pfanchri/Wordclock/Frontplatten/Glocke/File:Bell font awesome.svg - Wikimedia Commons.pdf

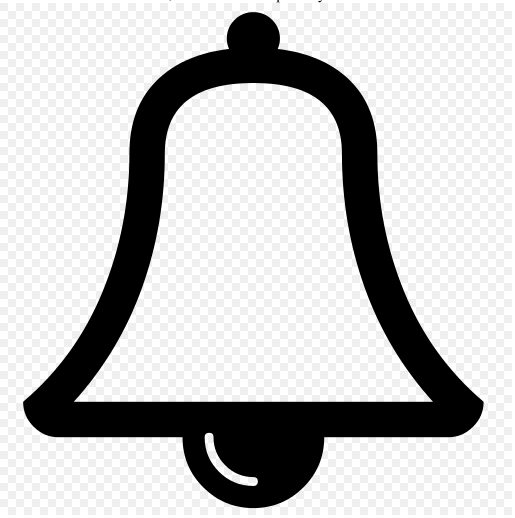
[picture p33: figure]

The source code of this SVG (https://commons.wikimedia.org/wiki/Help:SVG) is valid (https://validator.w3.org/check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). (https://validator.w3.org/check?ss=1)

This vector image (https://en.wikipedia.org/wiki/Vector_graphics) was created with Inkscape, (https://commons.wikimedia.org/wiki/Help:Inkscape) and then manually (https://en.wikipedia.org/wiki/Text_editor) edited.

# File:Bell font awesome.svg

From Wikimedia Commons, the free media repository

Size of this PNG preview of this SVG file: 512 × 512 pixels. (https://upload.wikimedia.org/wikipedia/commons/thumb/c/ca/Bell_font_awesome.svg/512px-Bell_font_awesome.svg.png)
Original file (https://upload.wikimedia.org/wikipedia/commons/c/ca/Bell_font_awesome.svg) (SVG file, nominally 512 × 512 pixels, file size: 2 KB)

This image rendered as PNG in other widths: 200px, (https://upload.wikimedia.org/wikipedia/commons/thumb/c/ca/Bell_font_awesome.svg/200px-Bell_font_awesome.svg.png) 500px, (https://upload.wikimedia.org/wikipedia/commons/thumb/c/ca/Bell_font_awesome.svg/500px-Bell_font_awesome.svg.png) 1000px, (https://upload.wikimedia.org/wikipedia/commons/thumb/c/ca/Bell_font_awesome.svg/1000px-Bell_font_awesome.svg.png) 2000px. (https://upload.wikimedia.org/wikipedia/commons/thumb/c/ca/Bell_font_awesome.svg/2000px-Bell_font_awesome.svg.png)

## Summary

Description | Icon extracted from [fortawesome.github.com/Font-Awesome/ Font-Awesome]

Date
Source | http://fortawesome.github.com/Font-Awesome/
Author | Dave Gandy
SVG development

## Licensing

This file is licensed under the Creative Commons (https://en.wikipedia.org/wiki/en:Creative_Commons) Attribution-Share Alike 3.0 Unported (https://creativecommons.org/licenses/by-sa/3.0/deed.en) license.

### Attribution: Font Awesome by Dave Gandy - http://fortawesome.github.com/Font-Awesome (http://fortawesome.github.com/Font-Awesome)

You are free:

Wikimedia Commons auf Deutsch (https://commons.wikimedia.org/wiki/File:Bell_font_awesome.svg#) | [x] (https://commons.wikimedia.org/wiki/File:Bell_font_awesome.svg#) Download (https://commons.wikimedia.org/wiki/File:Bell_font_awesome.svg#)
all sizes

Use this file (https://commons.wikimedia.org/wiki/File:Bell_font_awesome.svg#)
on the web

Use this file (https://commons.wikimedia.org/wiki/File:Bell_font_awesome.svg#)
on a wiki

Email a link (https://commons.wikimedia.org/wiki/File:Bell_font_awesome.svg#)
to this file

Information (https://commons.wikimedia.org/wiki/File:Bell_font_awesome.svg#)
about reusing

Open in Media Viewer (https://upload.wikimedia.org/wikipedia/commons/c/ca/Bell_font_awesome.svg)

to share – to copy, distribute and transmit the work to remix – to adapt the work

Under the following conditions:

attribution – You must attribute the work in the manner specified by the author or licensor (but not in any way that suggests that they endorse you or your use of the work).
share alike – If you alter, transform, or build upon this work, you may distribute the resulting work only under the same or similar license to this one.

[[Category:]]

## File history

Click on a date/time to view the file as it appeared at that time.

| Date/Time | Thumbnail | Dimensions | User | Comment
current | 20:30, 26 January 2013 (https://upload.wikimedia.org/wikipedia/commons/c/ca/Bell_font_awesome.svg) | | 512 × 512 (2 KB) | Kondicherry (https://commons.wikimedia.org/wiki/User:Kondicherry) (talk (https://commons.wikimedia.org/wiki/User_talk:Kondicherry) | contribs) (https://commons.wikimedia.org/wiki/Special:Contributions/Kondicherry) | VicuñaUploader 1.16

You cannot overwrite this file.

## File usage on Commons

The following page links to this file:

User:Kondicherry/gallery (https://commons.wikimedia.org/wiki/User:Kondicherry/gallery)

## Metadata

This file contains additional information, such as Exif (https://commons.wikimedia.org/wiki/Commons:Exif) metadata, probably added from the digital camera or scanner used to create or digitize it. If the file has been modified from its original state, some details may not fully reflect the modified file. The timestamp is only as accurate as the clock in the camera, and it may be completely wrong.

Retrieved from "https://commons.wikimedia.org/w/index.php?title=File:Bell_font_awesome.svg&oldid=144734182"

Categories: (https://commons.wikimedia.org/wiki/Special:Categories) Font-Awesome icons (https://commons.wikimedia.org/wiki/Category:Font-Awesome_icons) Bell icons (https://commons.wikimedia.org/wiki/Category:Bell_icons)

This page was last modified on 30 December 2014, at 15:17.
Text is available under the Creative Commons Attribution-ShareAlike License; (https://creativecommons.org/licenses/by-sa/3.0/) additional terms may apply. By using this site, you agree to the Terms of Use (https://wikimediafoundation.org/wiki/Terms_of_Use) and Privacy Policy. (https://wikimediafoundation.org/wiki/Privacy_policy)
