pfanchri/Wordclock/CAD/Bilder/Bildschirmfoto 2015-12-24 um 15.16.03.png

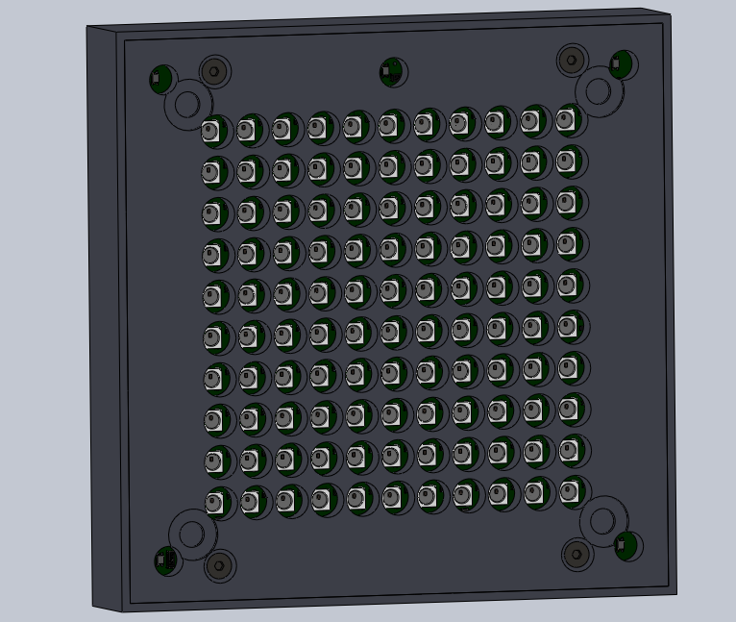
CAD/Bilder/Bildschirmfoto 2015-12-24 um 15.16.03.png
