pfanchri/Wordclock/CAD/Platine/Bauteile/importiert/ldr-cell-5mm-1.snapshot.6/Renderings/5mm-LDR-thru-hole-leaded.jpg

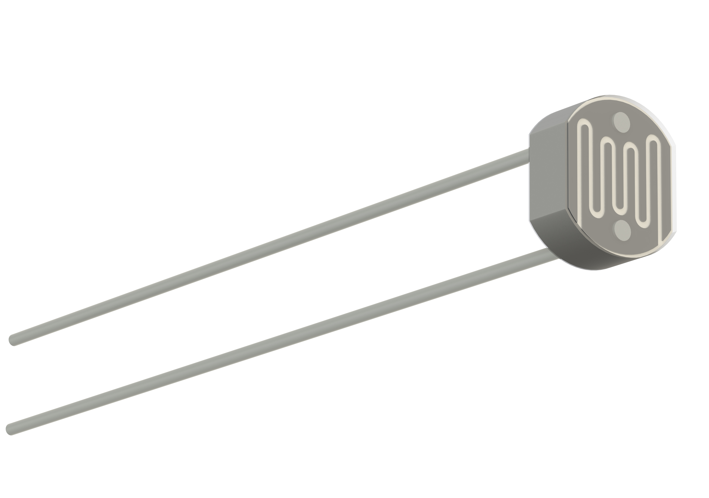
CAD/Platine/Bauteile/importiert/ldr-cell-5mm-1.snapshot.6/Renderings/5mm-LDR-thru-hole-leaded.jpg
