pfanchri/Wordclock/CAD/Platine/Bauteile/importiert/ldr-cell-5mm-1.snapshot.6/Renderings/LDR cell thru-hole leaded.jpg

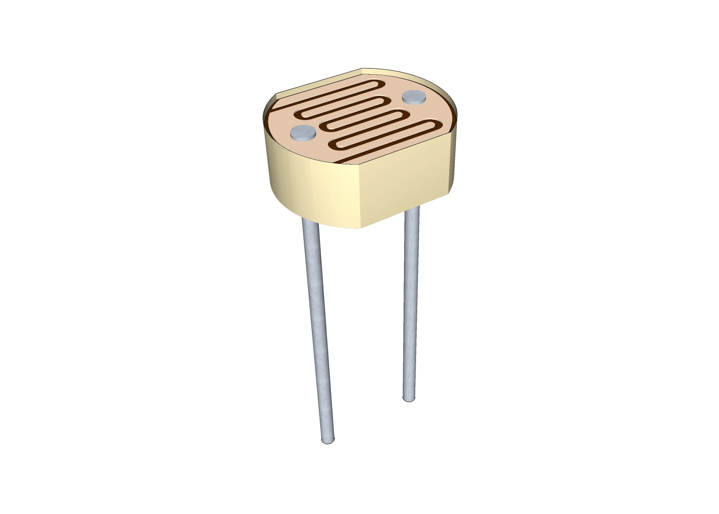
CAD/Platine/Bauteile/importiert/ldr-cell-5mm-1.snapshot.6/Renderings/LDR cell thru-hole leaded.jpg
