pfanchri/Wordclock/CAD/Platine/Bauteile/importiert/to220-to220ab-1.snapshot.5/Renderings/IMG_001.JPG

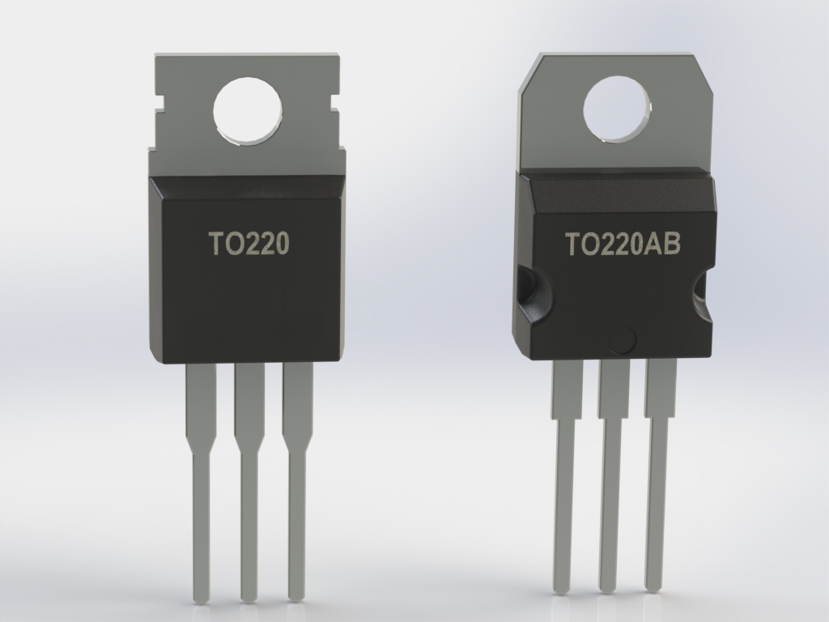
CAD/Platine/Bauteile/importiert/to220-to220ab-1.snapshot.5/Renderings/IMG_001.JPG
