pfanchri/Wordclock/Dokumentationen/Dokumentation/Bilder/SW1.png

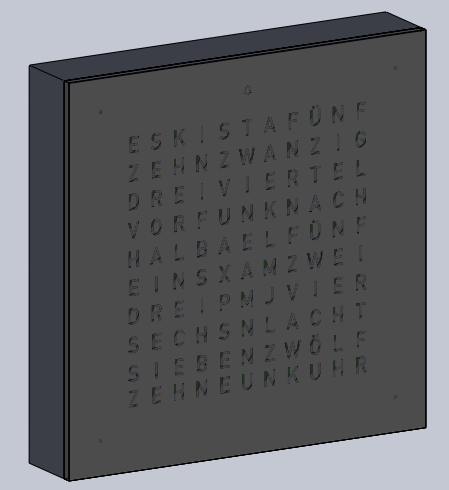
Dokumentationen/Dokumentation/Bilder/SW1.png
