pfanchri/Wordclock/Dokumentationen/Projektpräsentation/Anordnung3.png

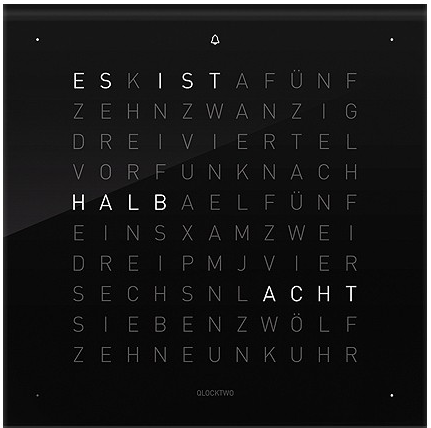
Dokumentationen/Projektpräsentation/Anordnung3.png
