pfanchri/Wordclock/Dokumentationen/Projektpräsentation/EagleL1.png

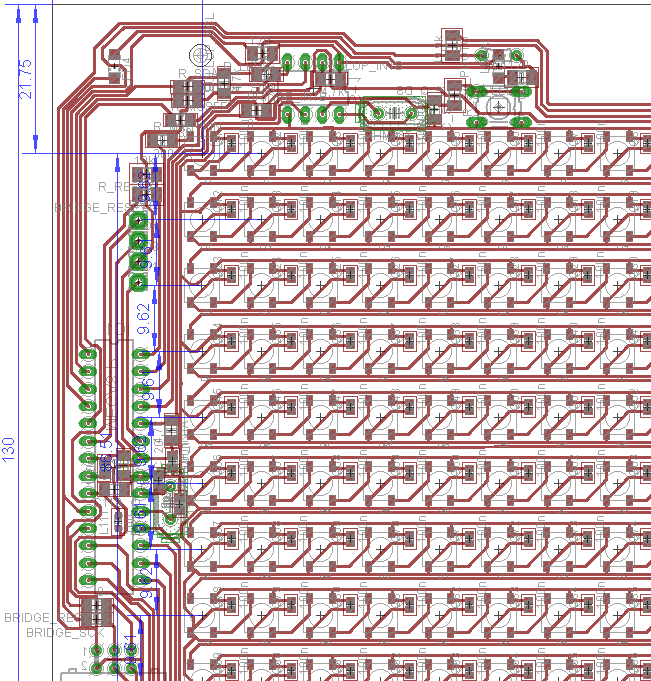
Dokumentationen/Projektpräsentation/EagleL1.png
