pfanchri/Wordclock/Dokumentationen/Projektpräsentation/EagleS2.png

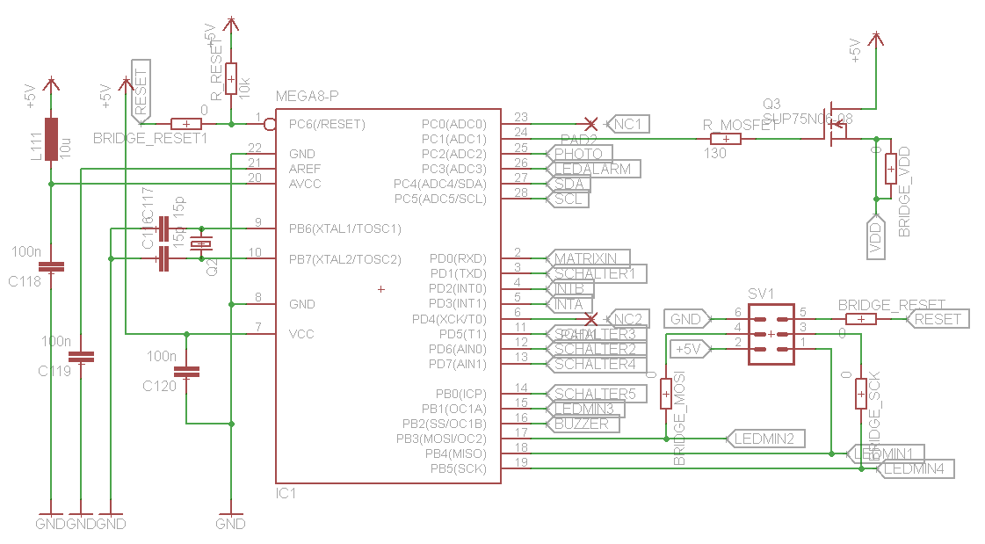
Dokumentationen/Projektpräsentation/EagleS2.png
