pfanchri/Wordclock/Dokumentationen/Projektpräsentation/SW3.png

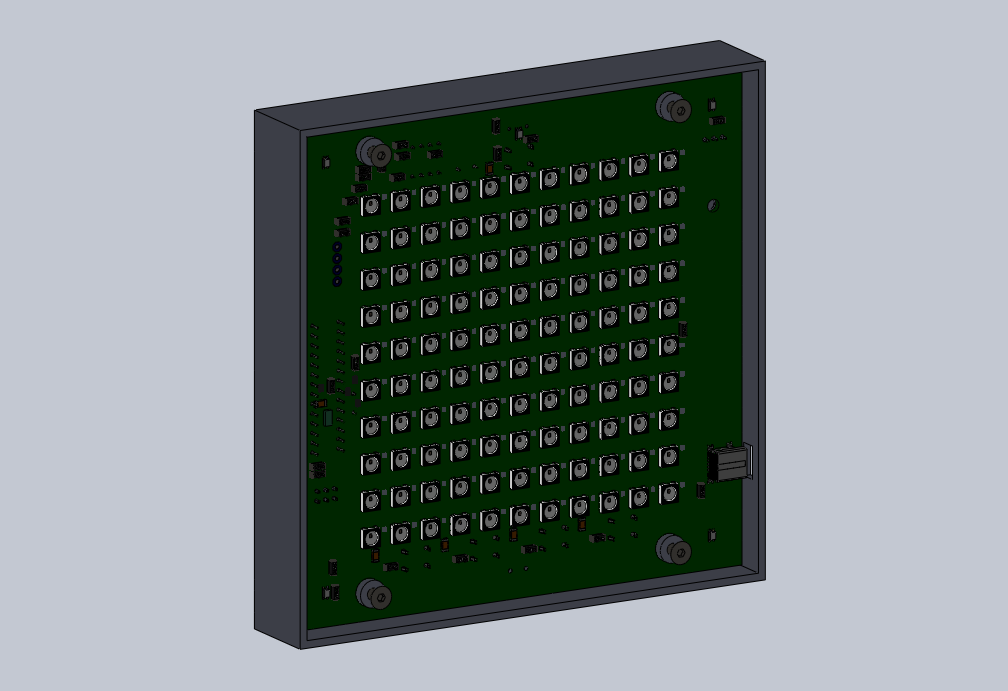
Dokumentationen/Projektpräsentation/SW3.png
