pfanchri/Wordclock/Frontplatten/Frontplatte Binär/Binäruhr/00addbfca08bbe93f4dcbb11746f65bc_1194087881.jpg

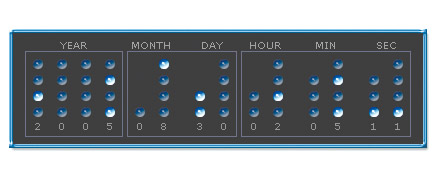
Frontplatten/Frontplatte Binär/Binäruhr/00addbfca08bbe93f4dcbb11746f65bc_1194087881.jpg
