pfanchri/Wordclock/Frontplatten/Frontplatte Binär/Binäruhr/68-847-74_2-original.png

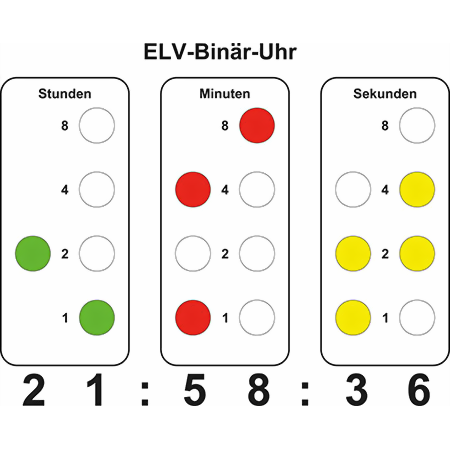
Frontplatten/Frontplatte Binär/Binäruhr/68-847-74_2-original.png
