pfanchri/Wordclock/Frontplatten/Frontplatte Binär/Binäruhr/500px-Binary_clock.png

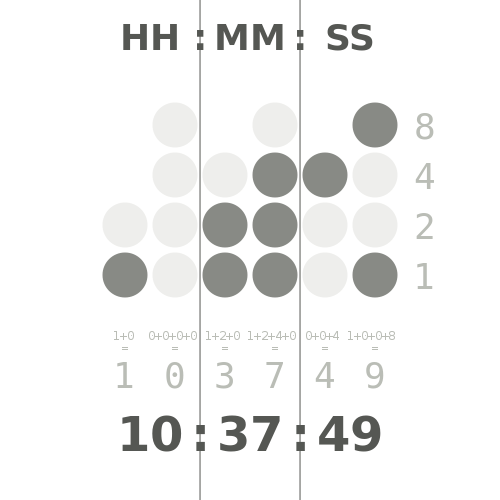
Frontplatten/Frontplatte Binär/Binäruhr/500px-Binary_clock.png
