pfanchri/Wordclock/Frontplatten/Wordclock-01.png

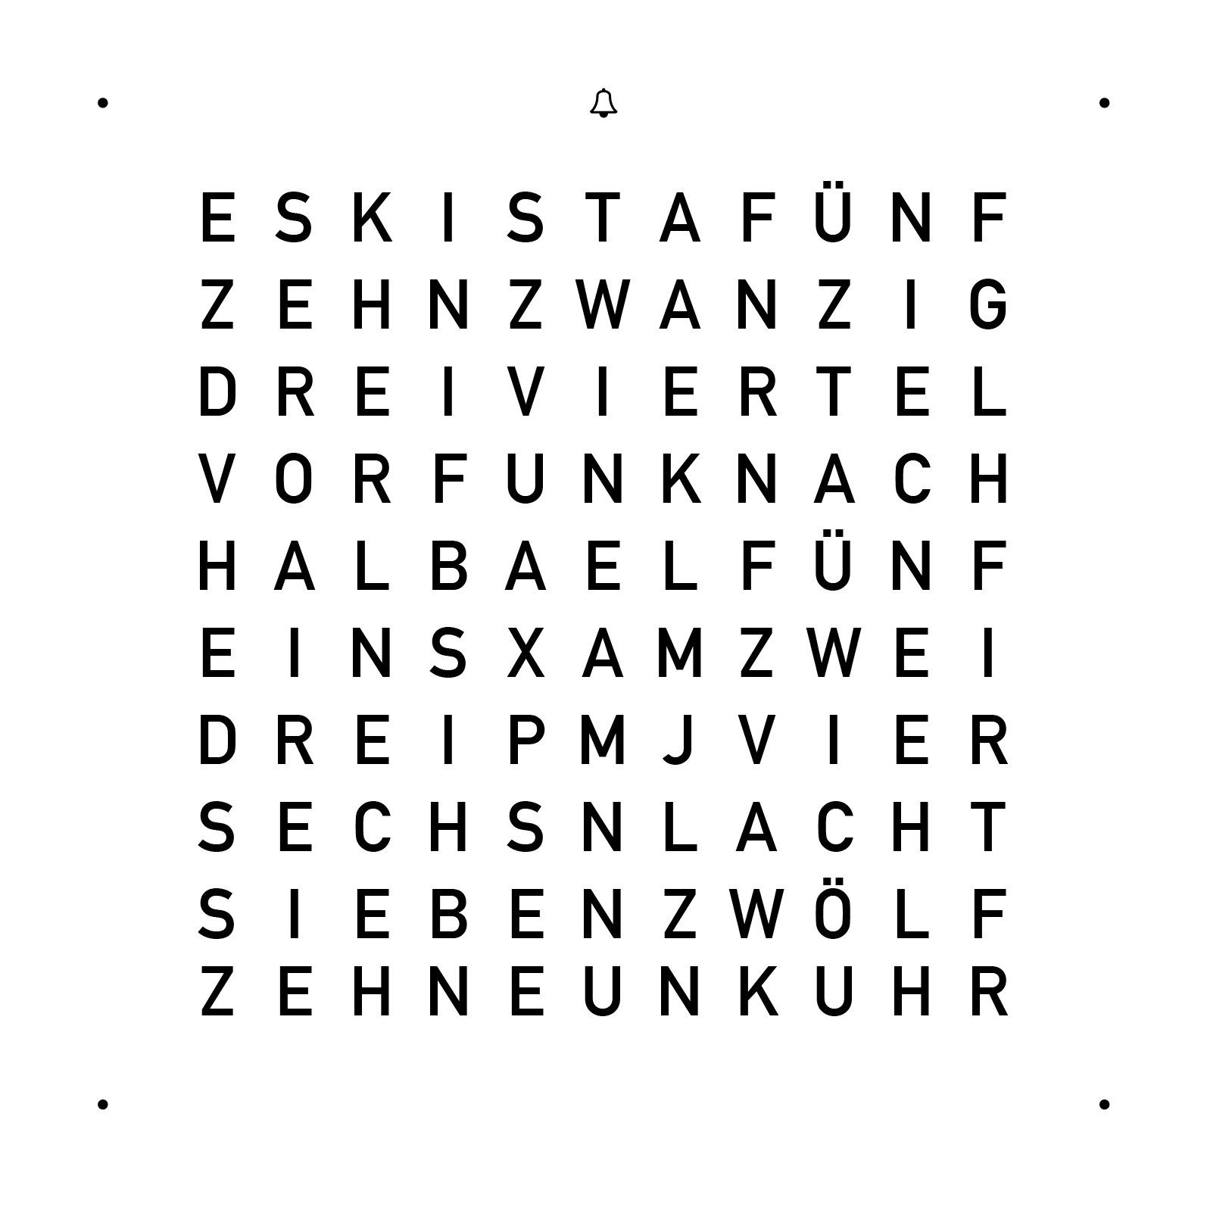
Frontplatten/Wordclock-01.png
