pfanchri/Wordclock/Pflichtenheft/images/0001.jpg

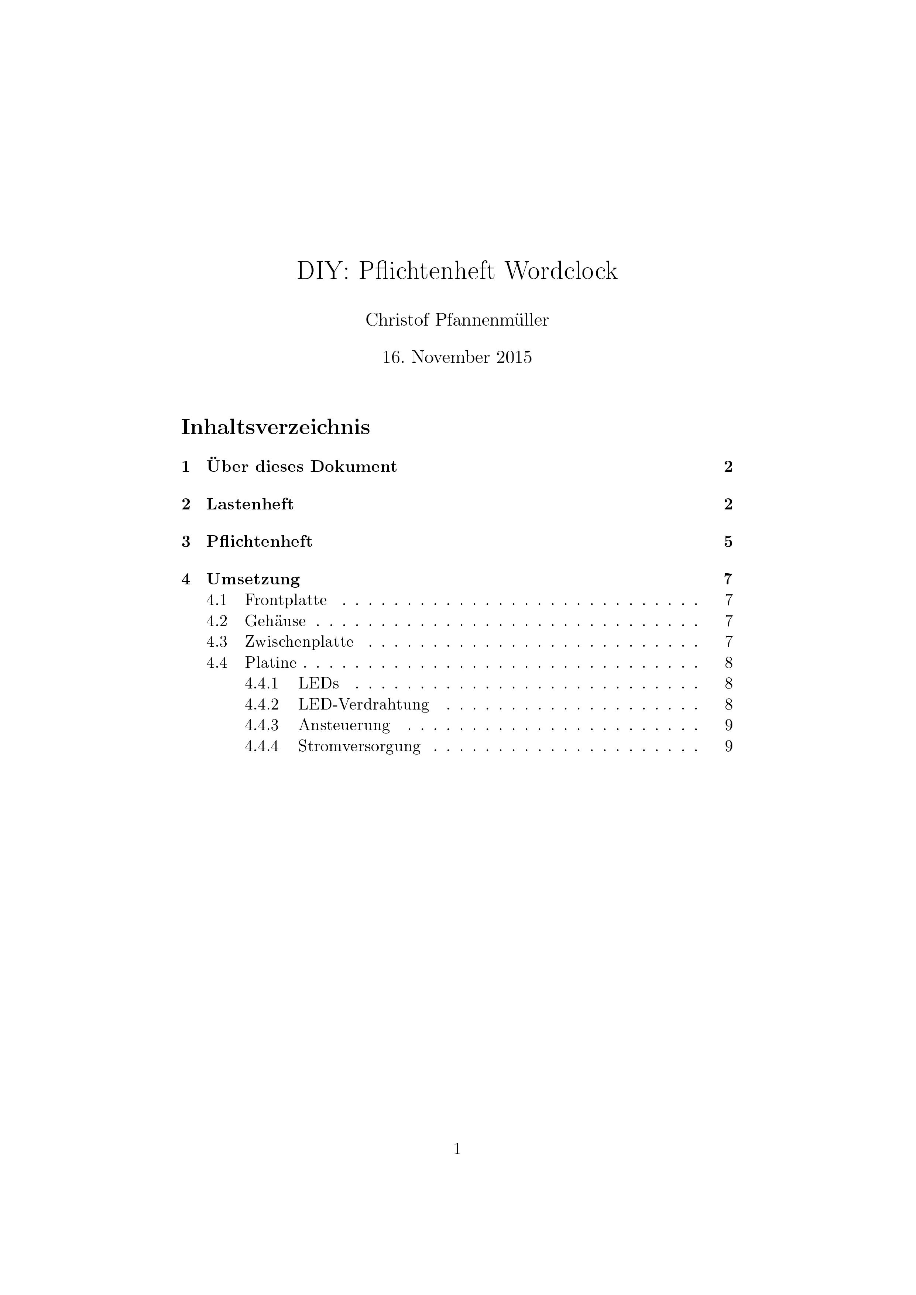
Pflichtenheft/images/0001.jpg
