pfanchri/Wordclock/Pflichtenheft/images/0002.jpg

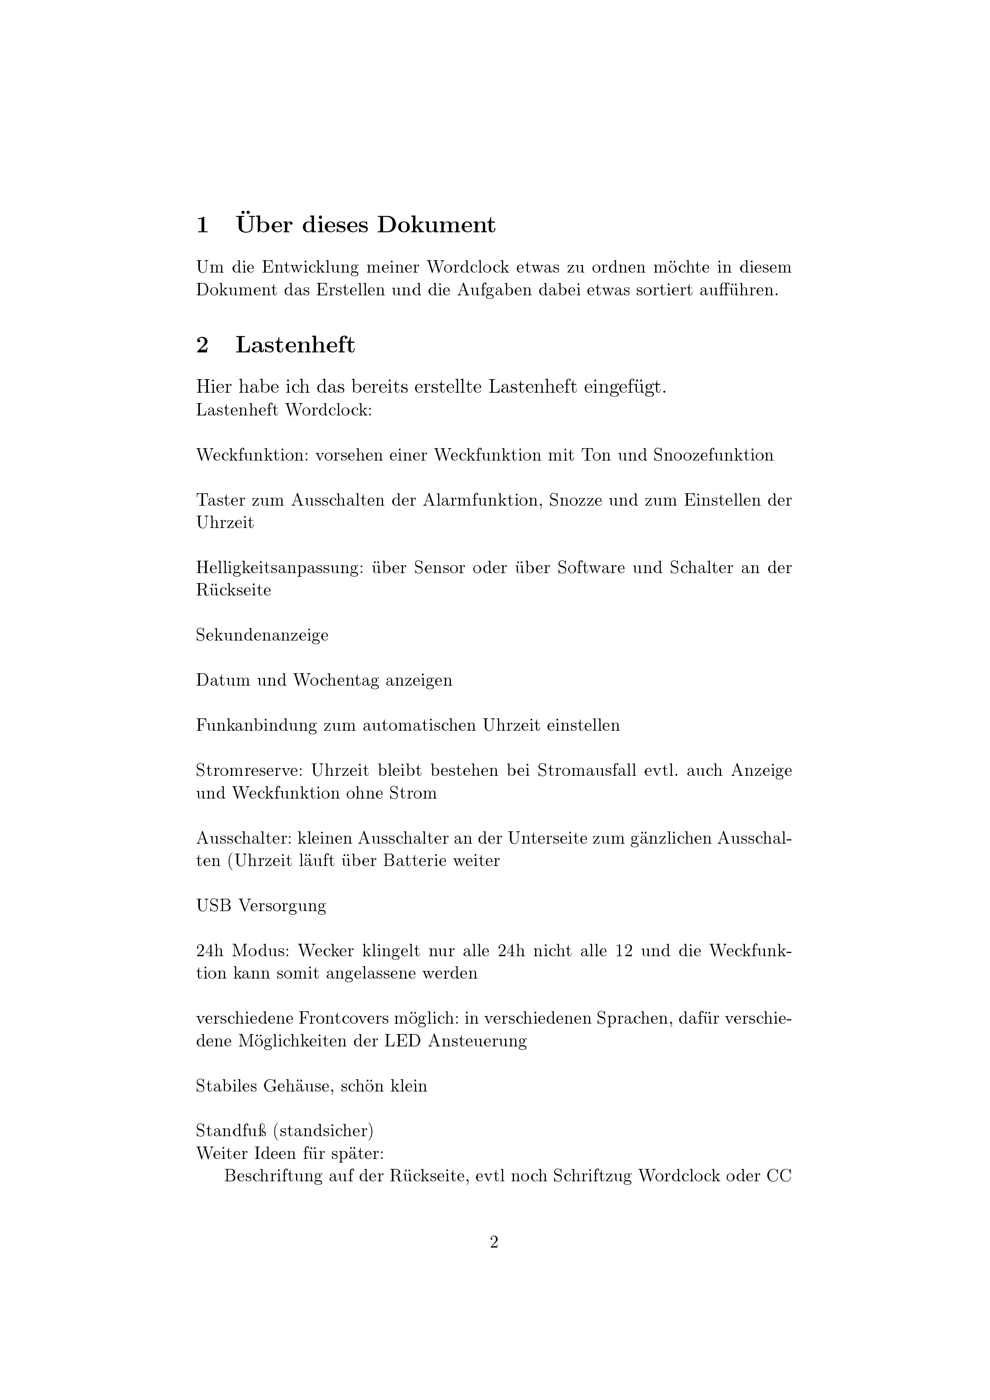
Pflichtenheft/images/0002.jpg
