pfanchri/Wordclock/Pflichtenheft/images/0005.jpg

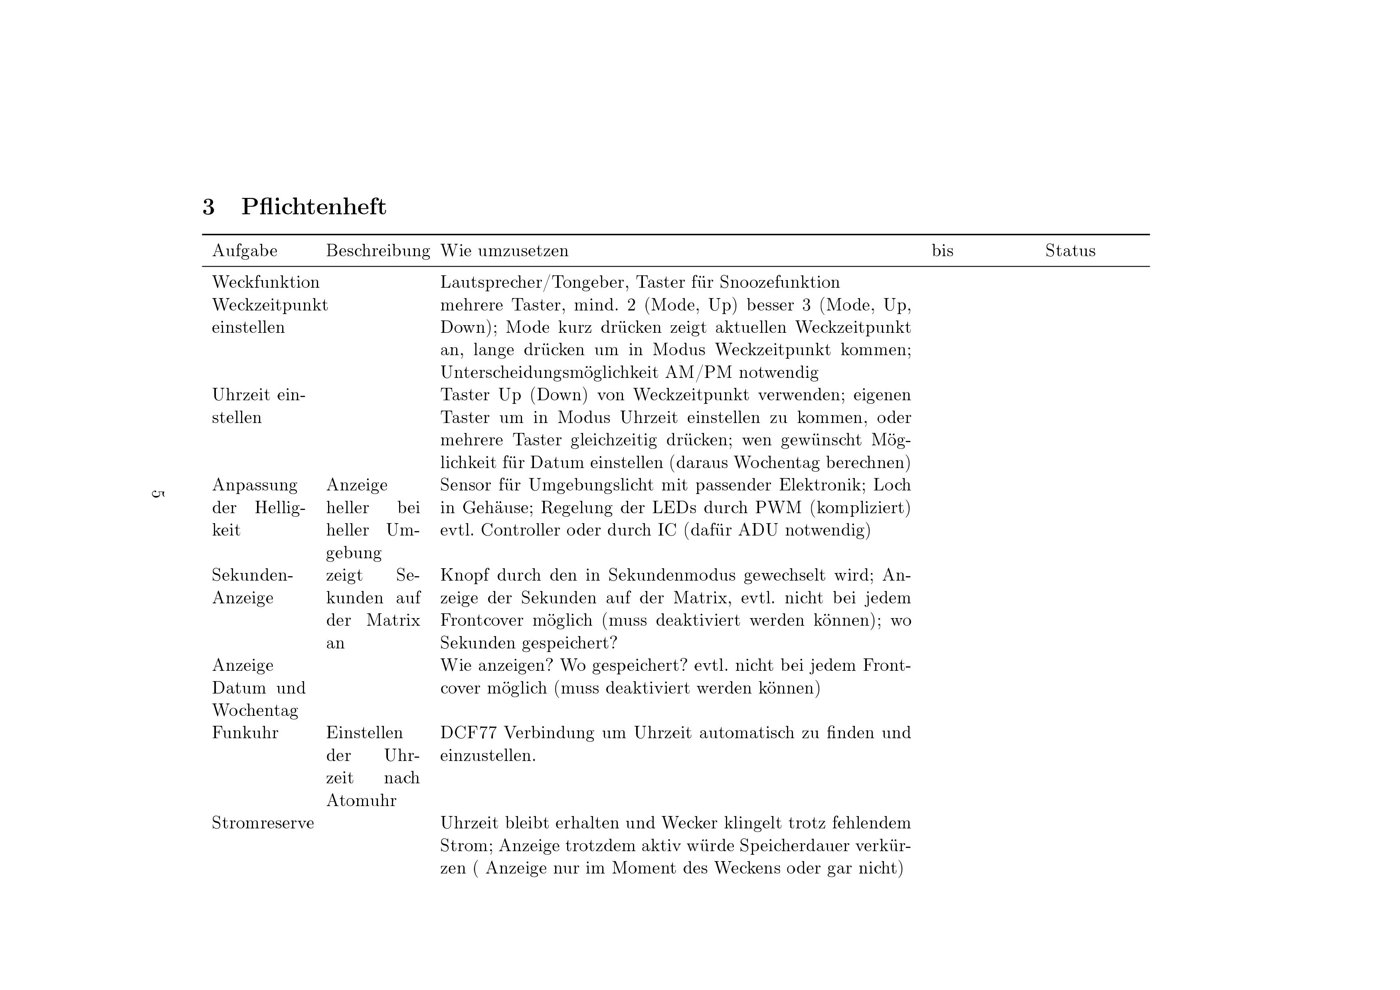
Pflichtenheft/images/0005.jpg
