pfanchri/Wordclock/Pflichtenheft/images/0006.jpg

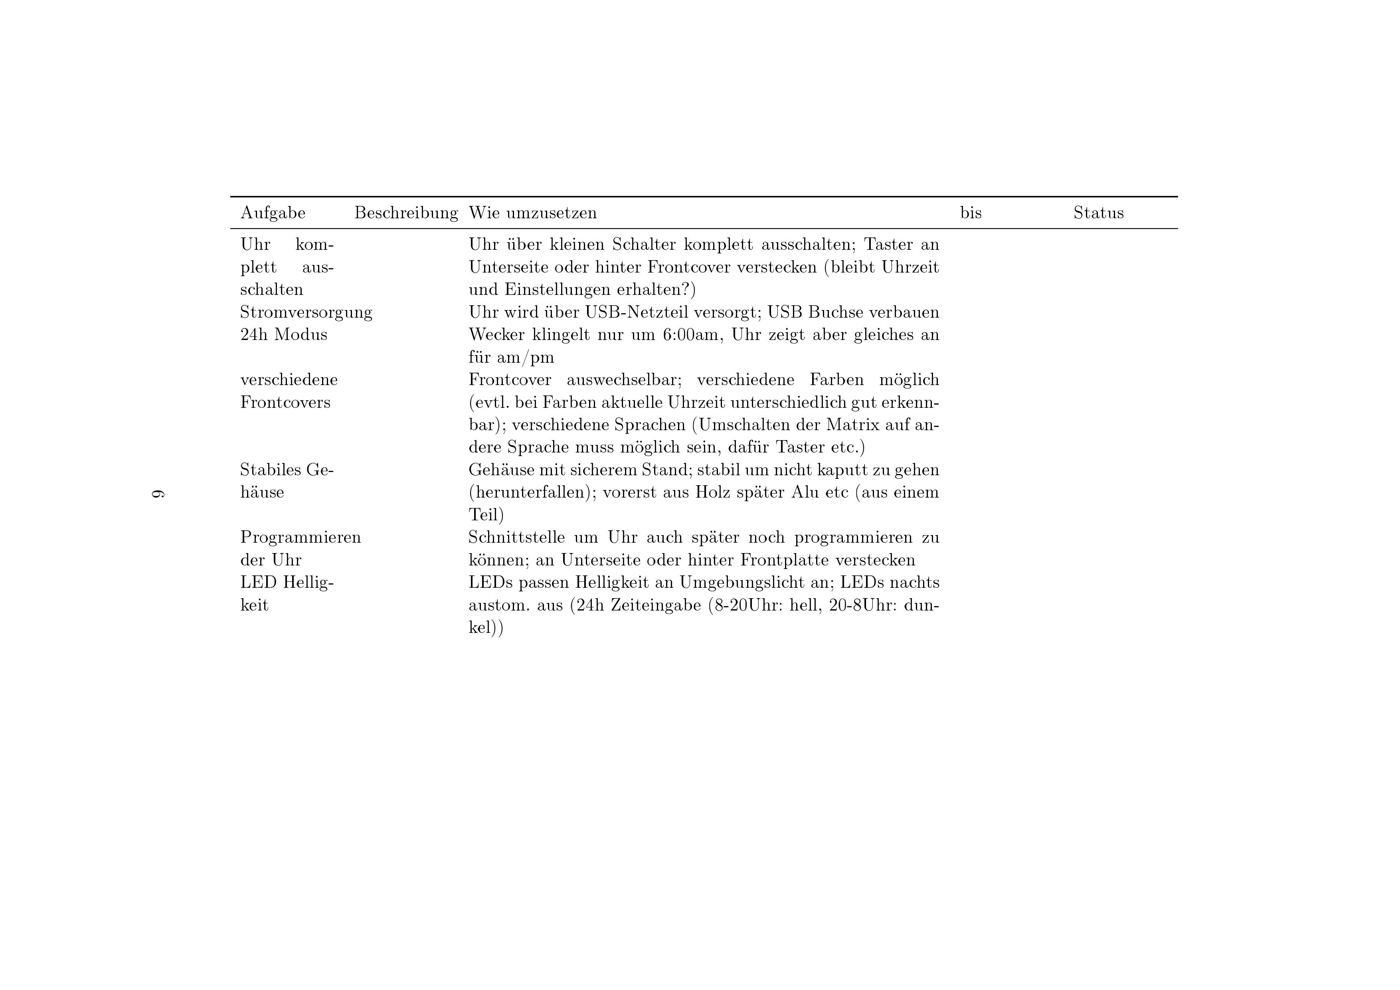
Pflichtenheft/images/0006.jpg
