pfanchri/Wordclock/Pflichtenheft/images/0007.jpg

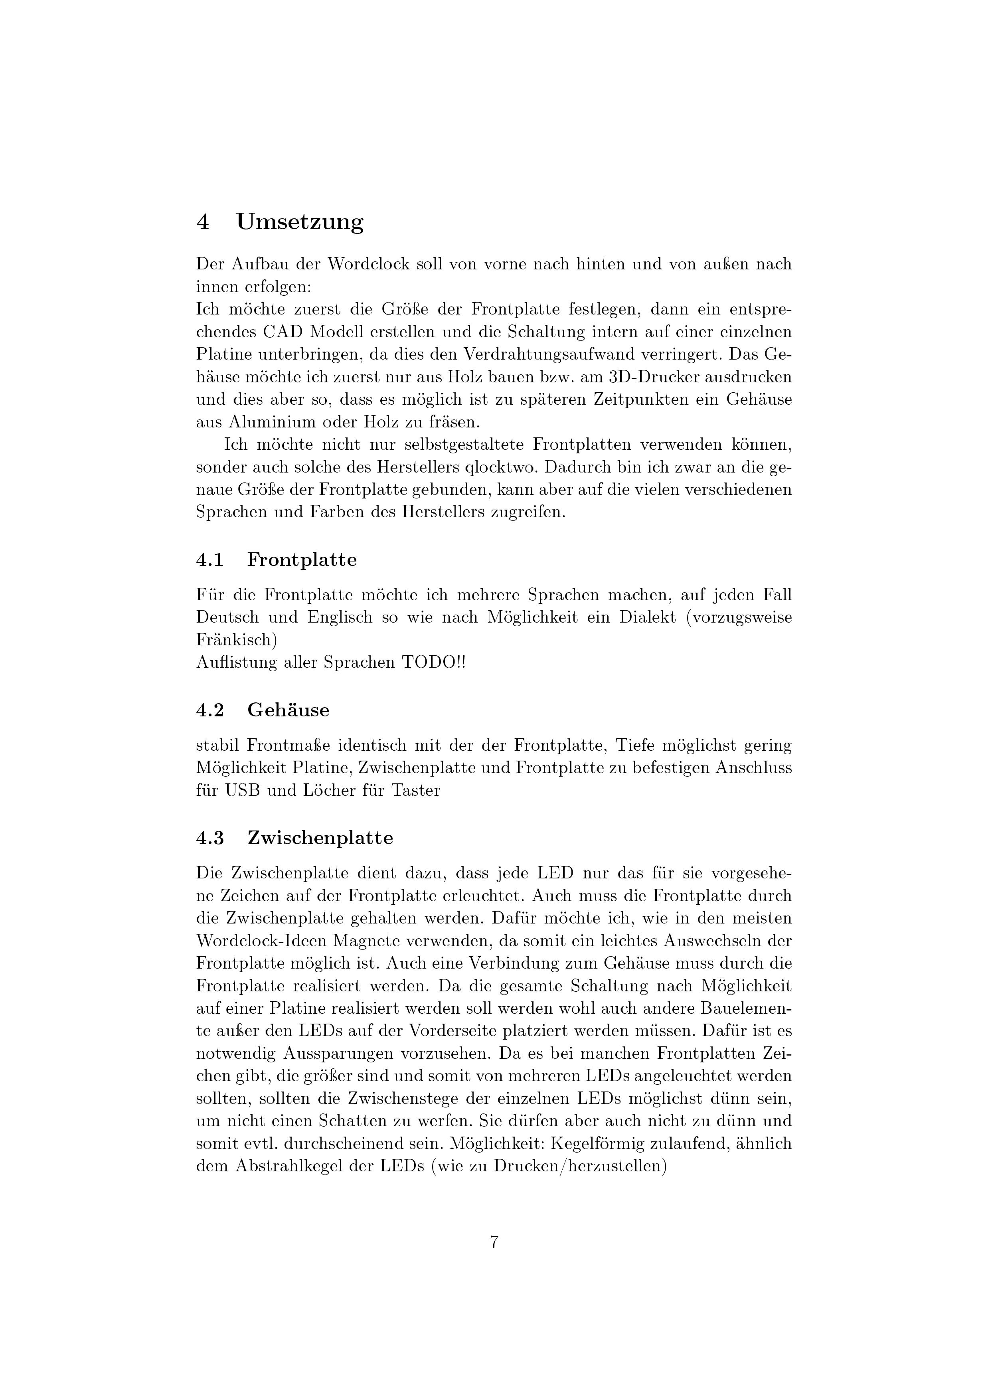
Pflichtenheft/images/0007.jpg
