pfanchri/Wordclock/Pflichtenheft/images/0008.jpg

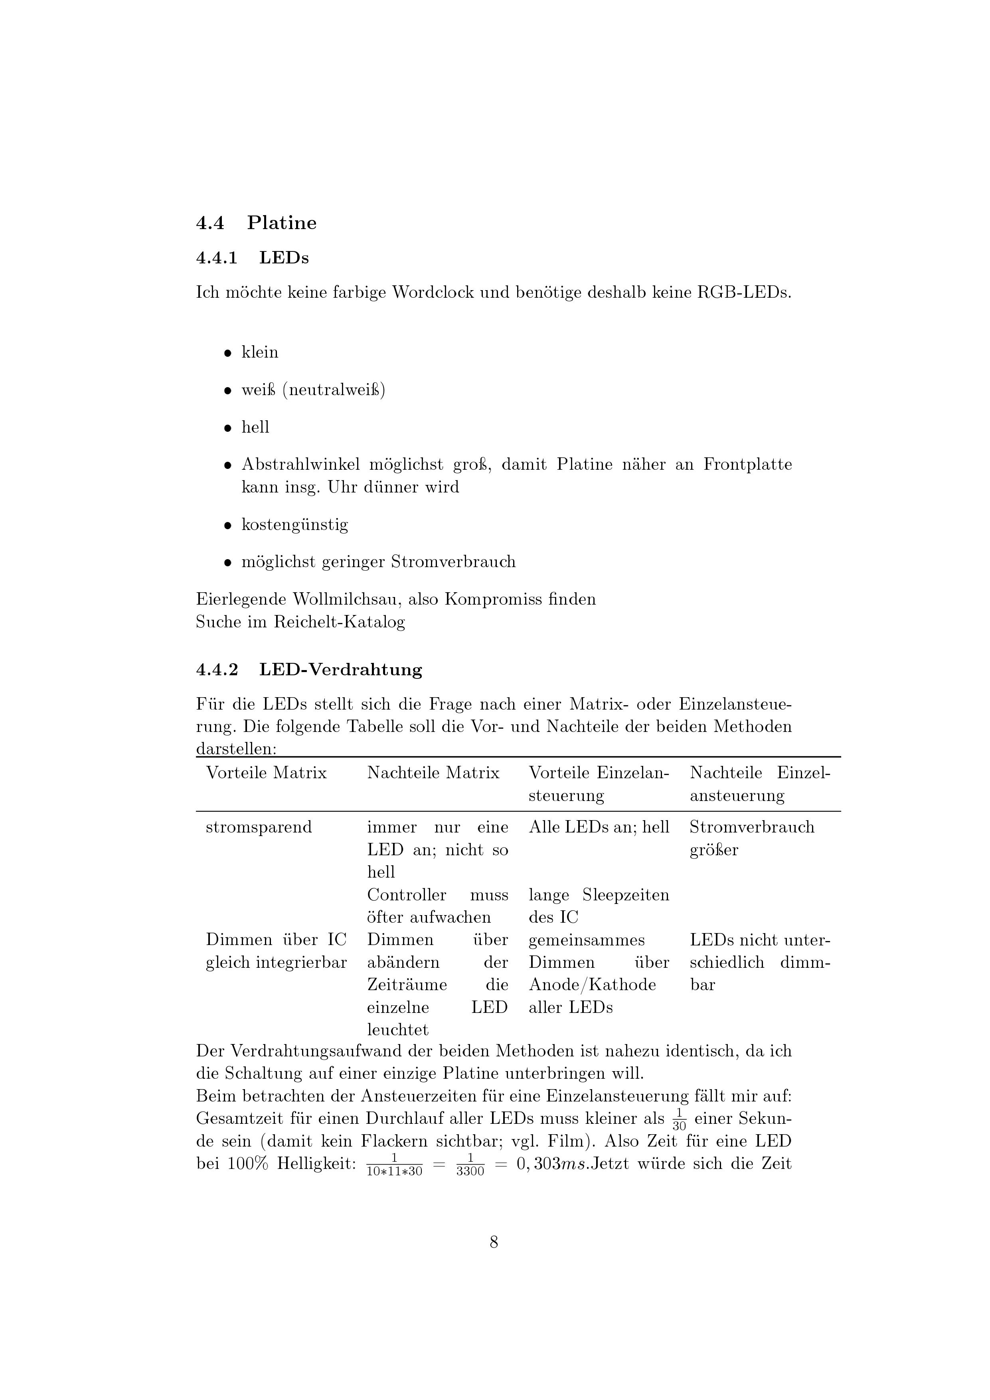
Pflichtenheft/images/0008.jpg
