pfanchri/Wordclock/Pflichtenheft/images/0009.jpg

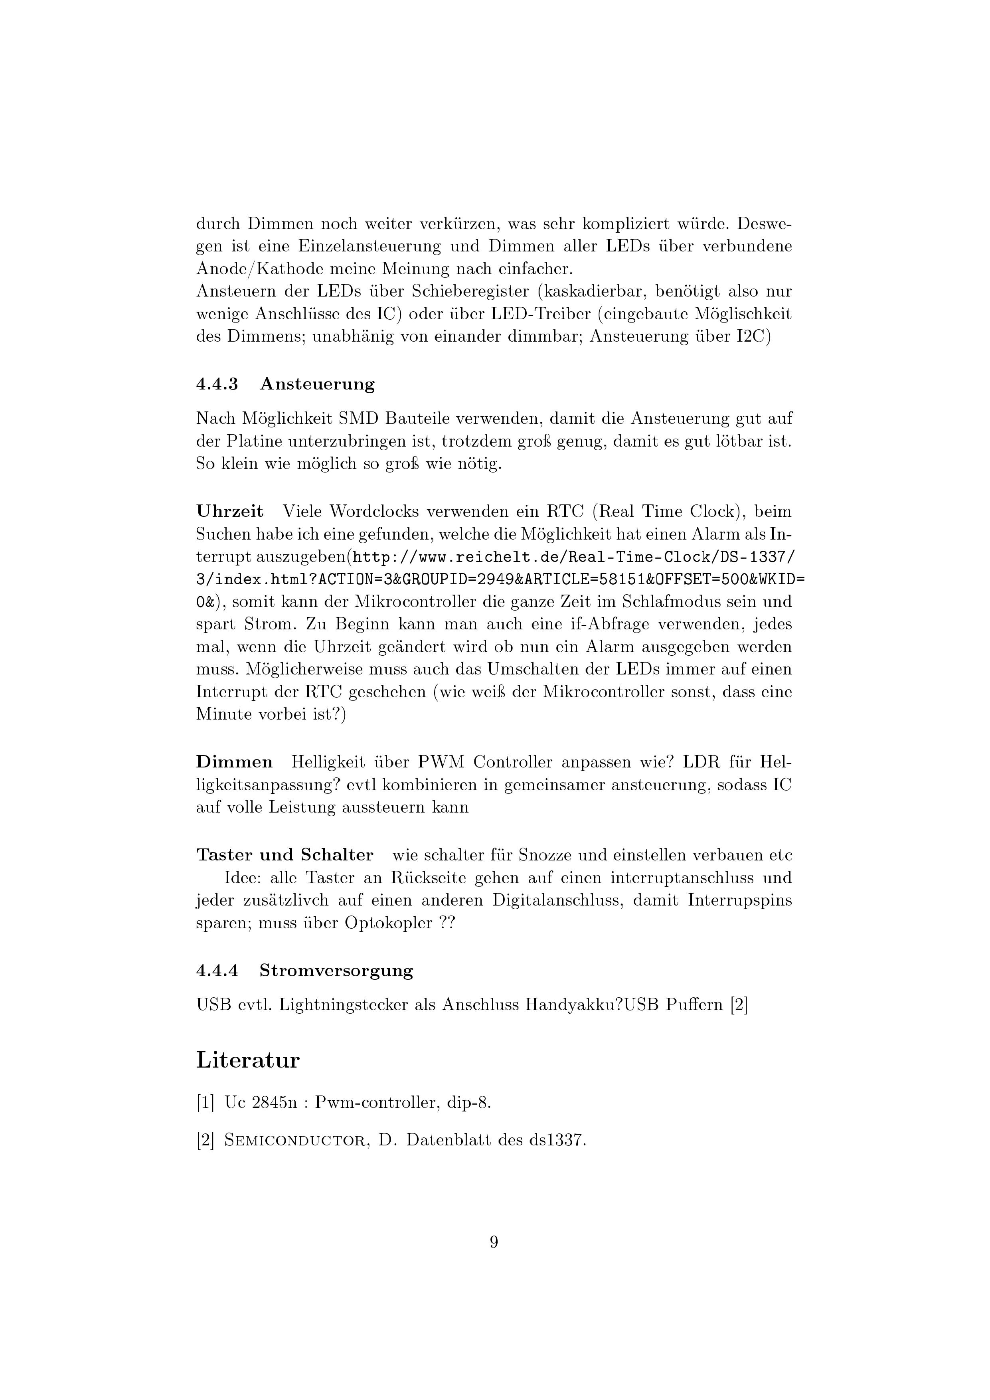
Pflichtenheft/images/0009.jpg
