pfanchri/Wordclock/Fertigungsdateien Fablab/Reflow/Schablone Lötpaste.dxf

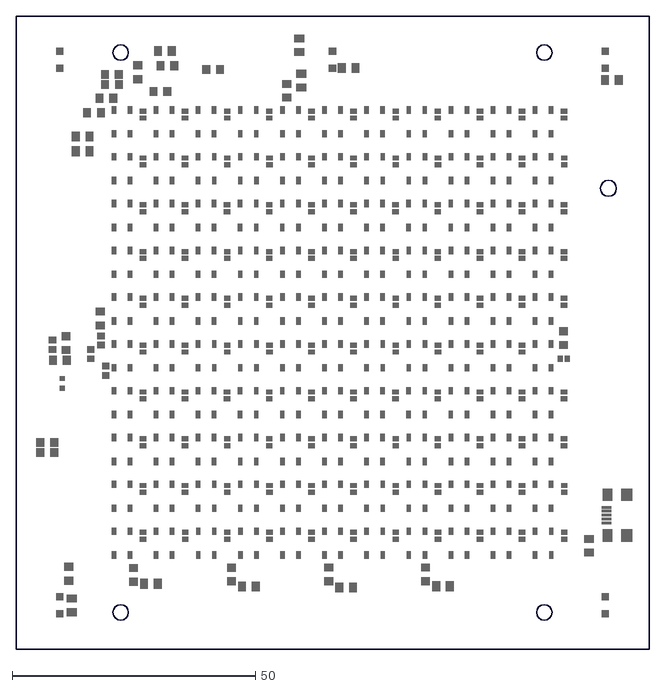
[picture p74: CAD file, 2016-01-13]
Fertigungsdateien Fablab/Reflow/Schablone Lötpaste.dxf
130.0 x 130.0
