pfanchri/Wordclock/CAD/Normteile/Innensechskant M3x10 Meusburger.SLDPRT

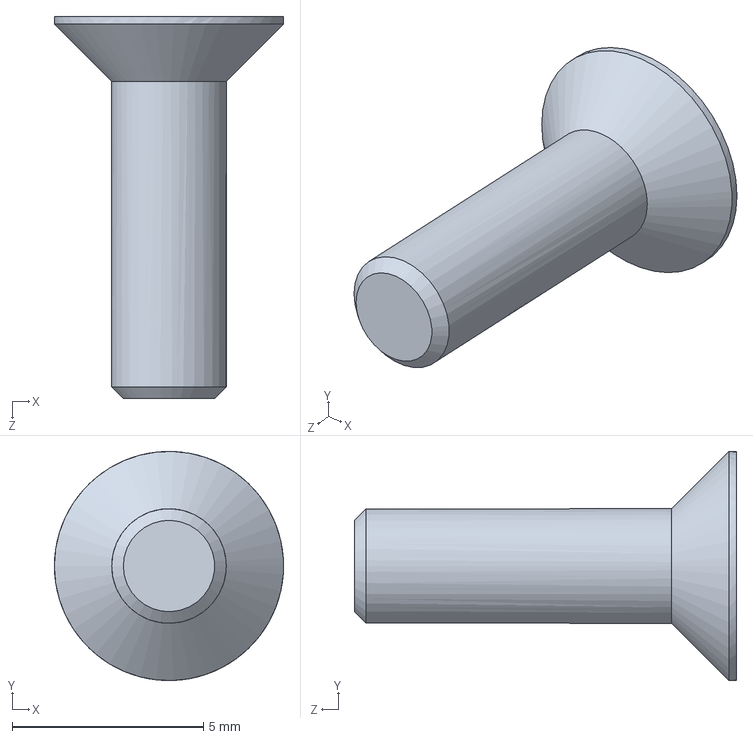
[picture p75: CAD file, 2015-12-24]
CAD/Normteile/Innensechskant M3x10 Meusburger.SLDPRT
6.00 x 6.00 x 10.0 mm
