pfanchri/Wordclock/CAD/Platine/Bauteile/importiert/ldr-cell-5mm-1.snapshot.6/LDR cell thru-hole leaded.STEP

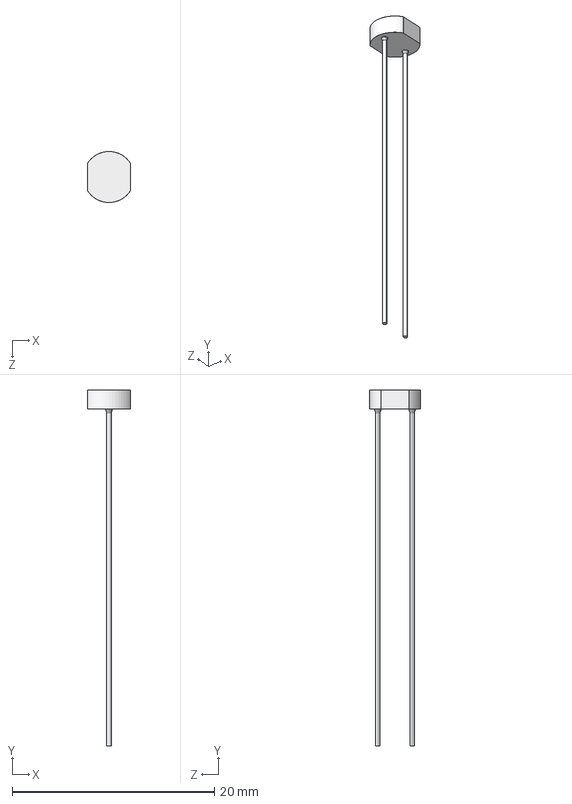
[picture p76: CAD file, 2015-12-23]
CAD/Platine/Bauteile/importiert/ldr-cell-5mm-1.snapshot.6/LDR cell thru-hole leaded.STEP
4.25 x 35.2 x 5.05 mm
Ceramic base^LDR cell thru-hole leaded
Electrodes^LDR cell thru-hole leaded
Leads^LDR cell thru-hole leaded
Part16^LDR cell thru-hole leaded
