pfanchri/Wordclock/CAD/Zwischenplatte.sldprt

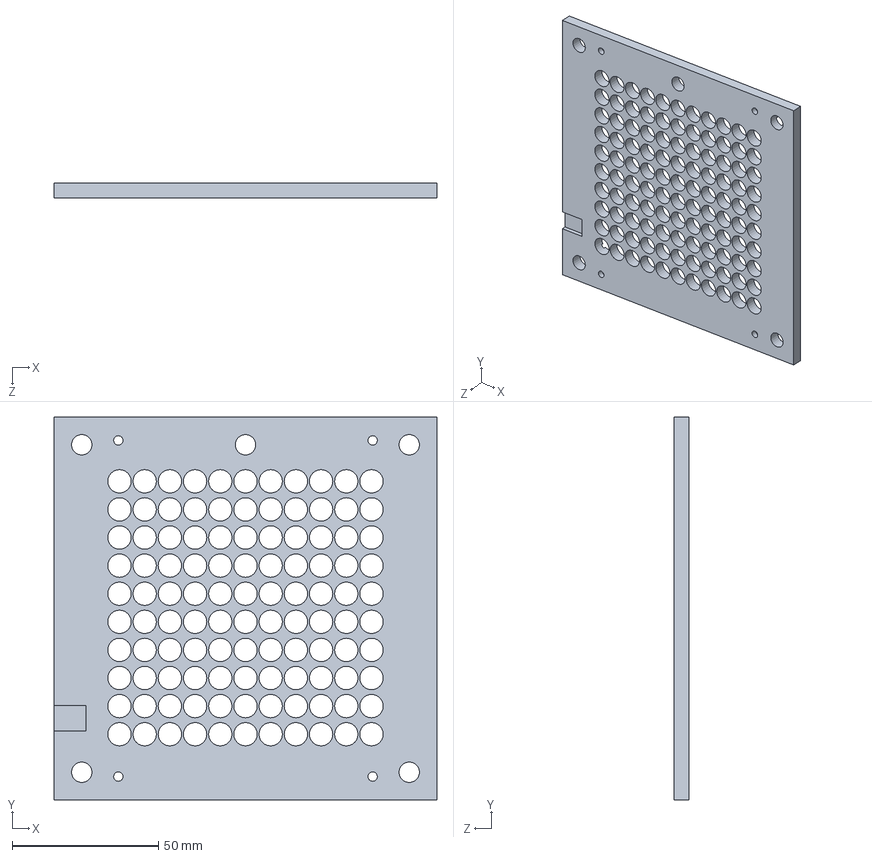
[picture p77: CAD file, 2016-01-15]
CAD/Zwischenplatte.sldprt
131.0 x 131.0 x 5.00 mm
