pfanchri/Wordclock/CAD/CircuitWorks/Komponenten/C1310_C1310.sldprt

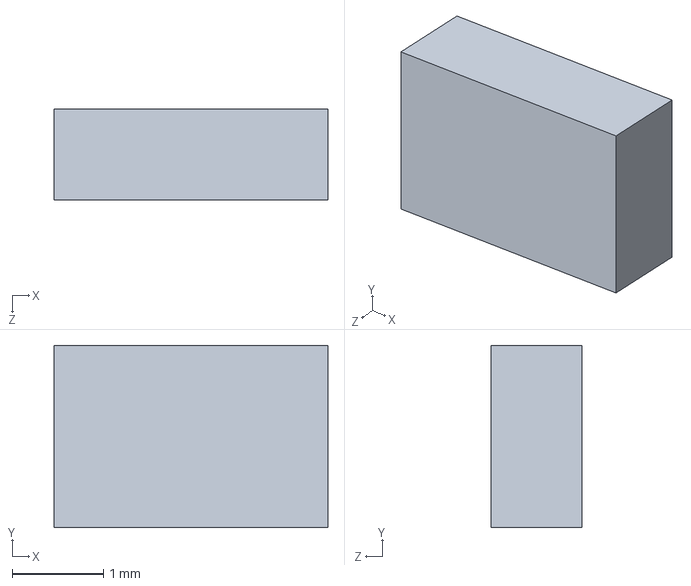
[picture p78: CAD file, 2015-12-23]
CAD/CircuitWorks/Komponenten/C1310_C1310.sldprt
3.00 x 1.99 x 1.00 mm
