pfanchri/Wordclock/CAD/GEhäuse.sldprt

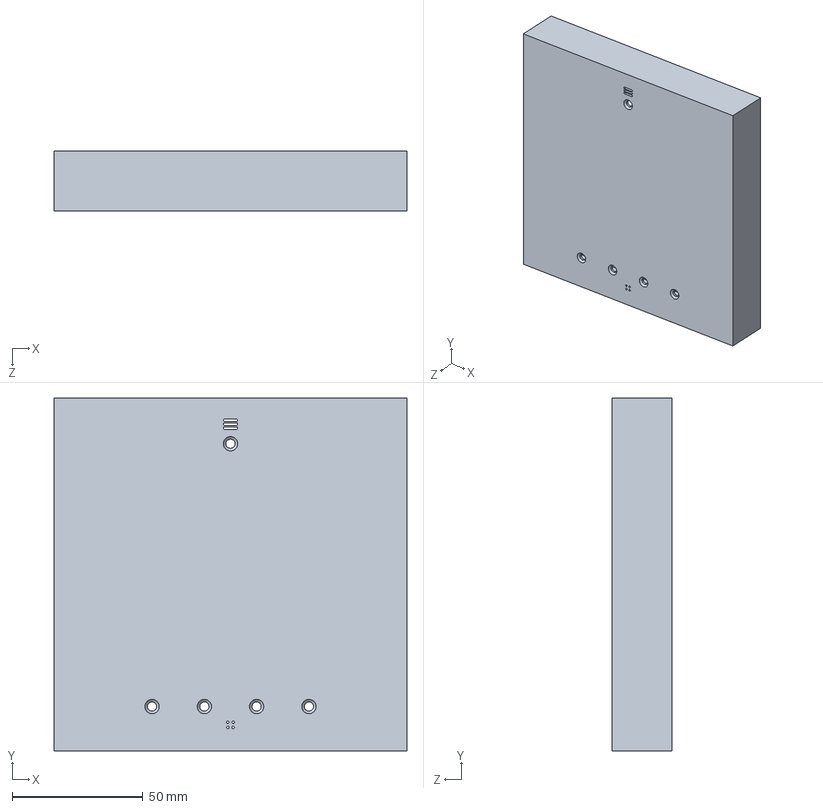
[picture p79: CAD file, 2016-01-15]
CAD/GEhäuse.sldprt
135.0 x 135.0 x 23.0 mm
