pfanchri/Wordclock/CAD/Platine/Bauteile/importiert/to220-to220ab-1.snapshot.5/TO220 - TO220AB.STEP

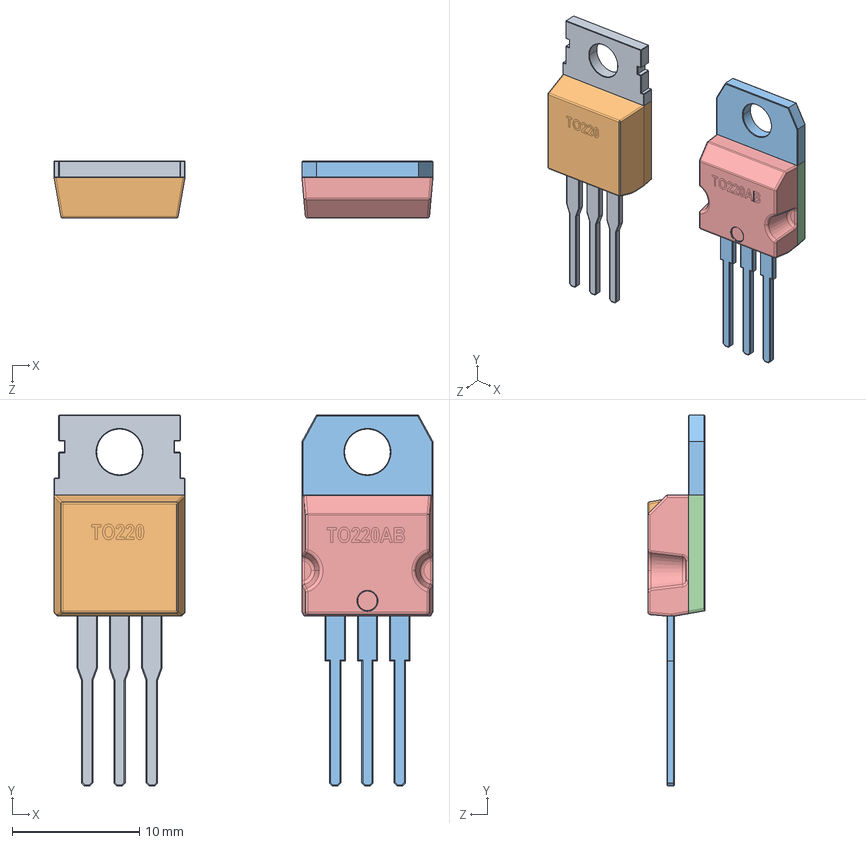
[picture p80: CAD file, 2015-12-23]
CAD/Platine/Bauteile/importiert/to220-to220ab-1.snapshot.5/TO220 - TO220AB.STEP
29.8 x 29.1 x 4.51 mm
TO220
TO220AB
