pfanchri/Wordclock/CAD/Platine/Bauteile/Signalgeber.SLDPRT

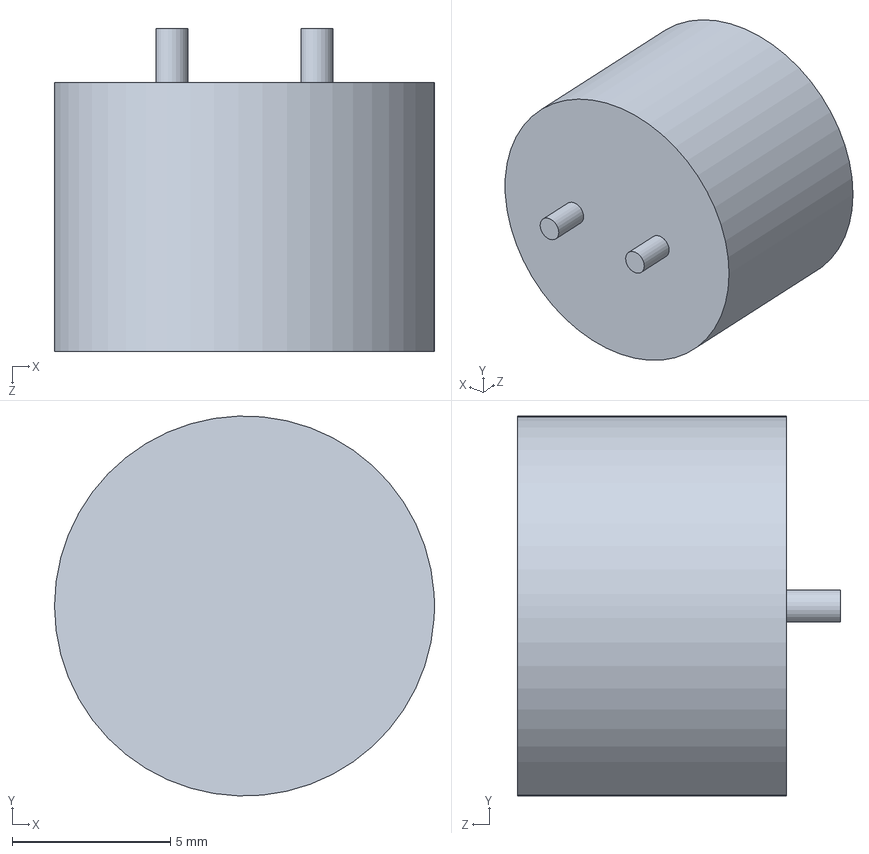
[picture p81: CAD file, 2015-12-23]
CAD/Platine/Bauteile/Signalgeber.SLDPRT
12.0 x 12.0 x 10.2 mm
