pfanchri/Wordclock/CAD/Abstandshalter Plastik.SLDPRT

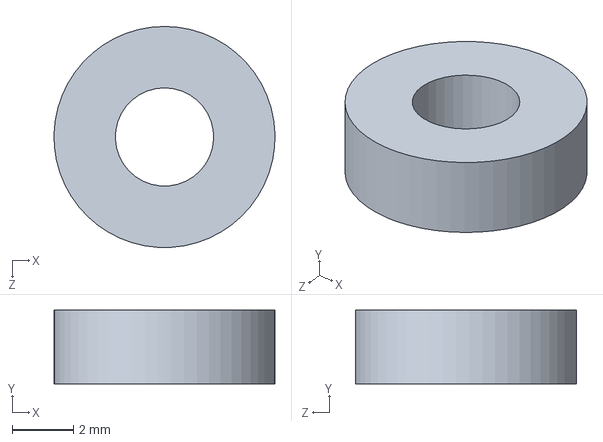
[picture p82: CAD file, 2015-12-24]
CAD/Abstandshalter Plastik.SLDPRT
7.20 x 2.40 x 7.20 mm
