pfanchri/Wordclock/CAD/Platine/Bauteile/Pad.SLDPRT

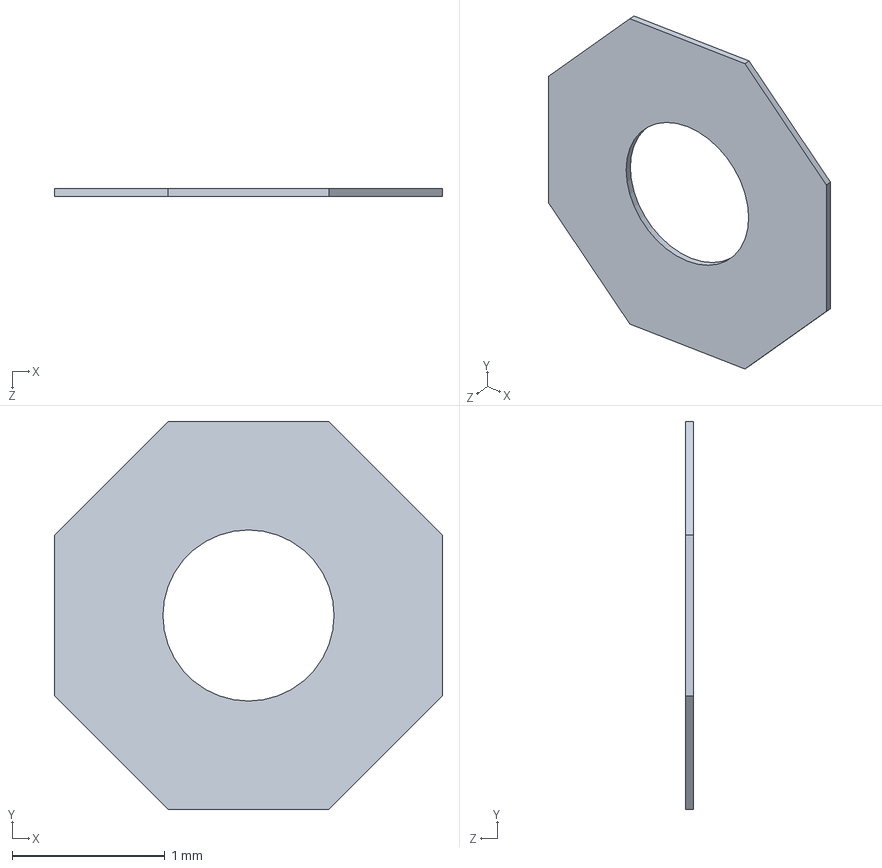
[picture p83: CAD file, 2015-12-23]
CAD/Platine/Bauteile/Pad.SLDPRT
2.54 x 2.54 x 0.05 mm
