pfanchri/Wordclock/CAD/Platine/Bauteile/ISP Stecker.SLDPRT

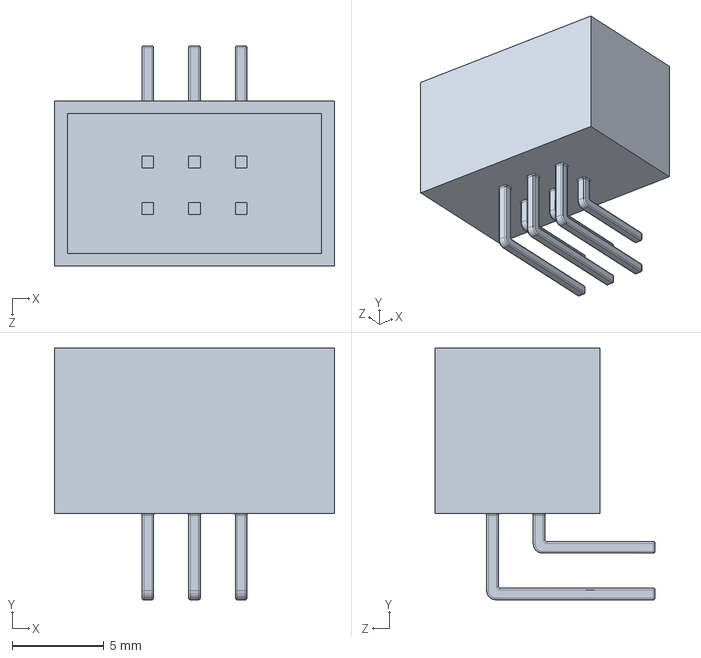
[picture p84: CAD file, 2015-12-23]
CAD/Platine/Bauteile/ISP Stecker.SLDPRT
15.2 x 13.7 x 12.0 mm
