pfanchri/Wordclock/CAD/Platine/Bauteile/Mini USB.SLDPRT

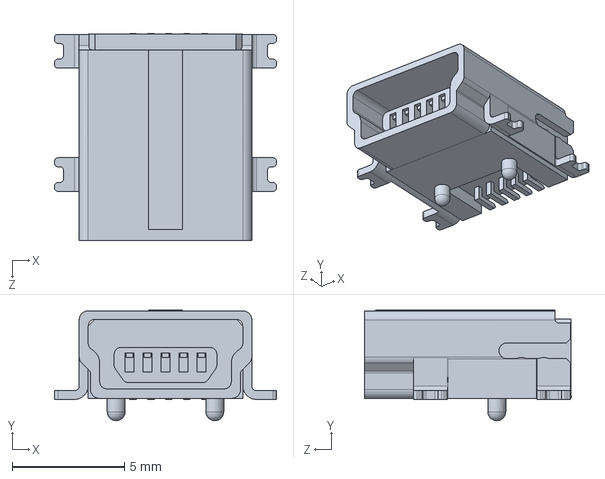
[picture p85: CAD file, 2015-12-23]
CAD/Platine/Bauteile/Mini USB.SLDPRT
9.90 x 4.93 x 9.25 mm
