pfanchri/Wordclock/CAD/Platine/Bauteile/HC49.SLDPRT

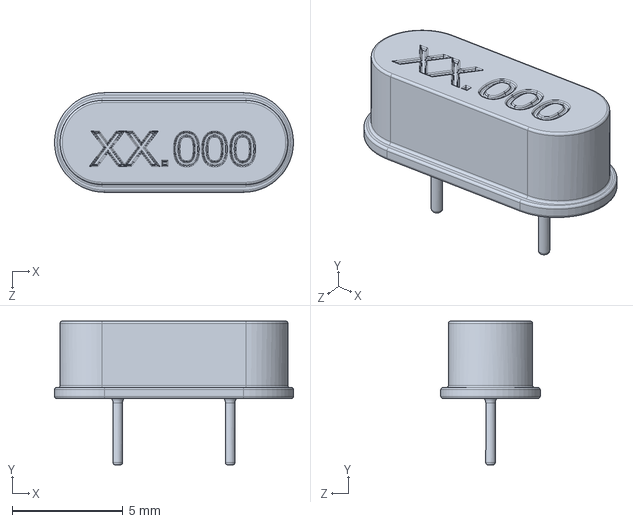
[picture p86: CAD file, 2015-12-23]
CAD/Platine/Bauteile/HC49.SLDPRT
10.8 x 6.50 x 4.50 mm
