pfanchri/Wordclock/CAD/Platine/Bauteile/LED1206.SLDPRT

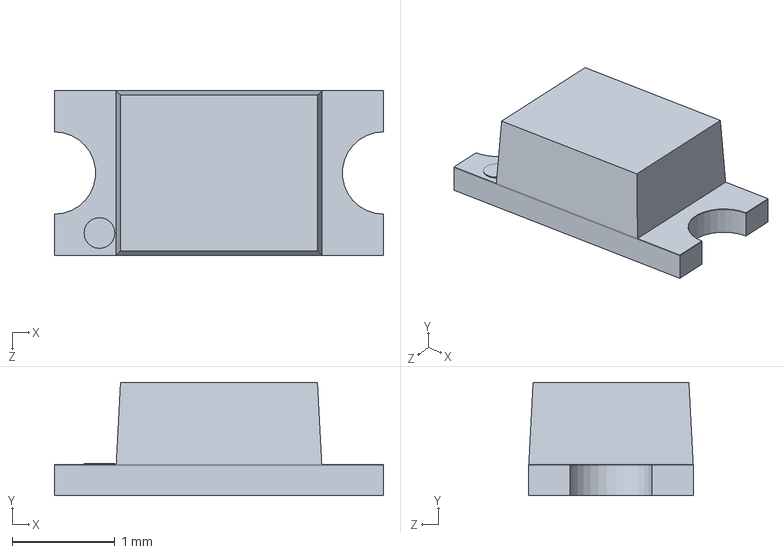
[picture p87: CAD file, 2015-12-23]
CAD/Platine/Bauteile/LED1206.SLDPRT
3.20 x 1.10 x 1.60 mm
