pfanchri/Wordclock/CAD/Platine/Bauteile/DIP8.SLDPRT

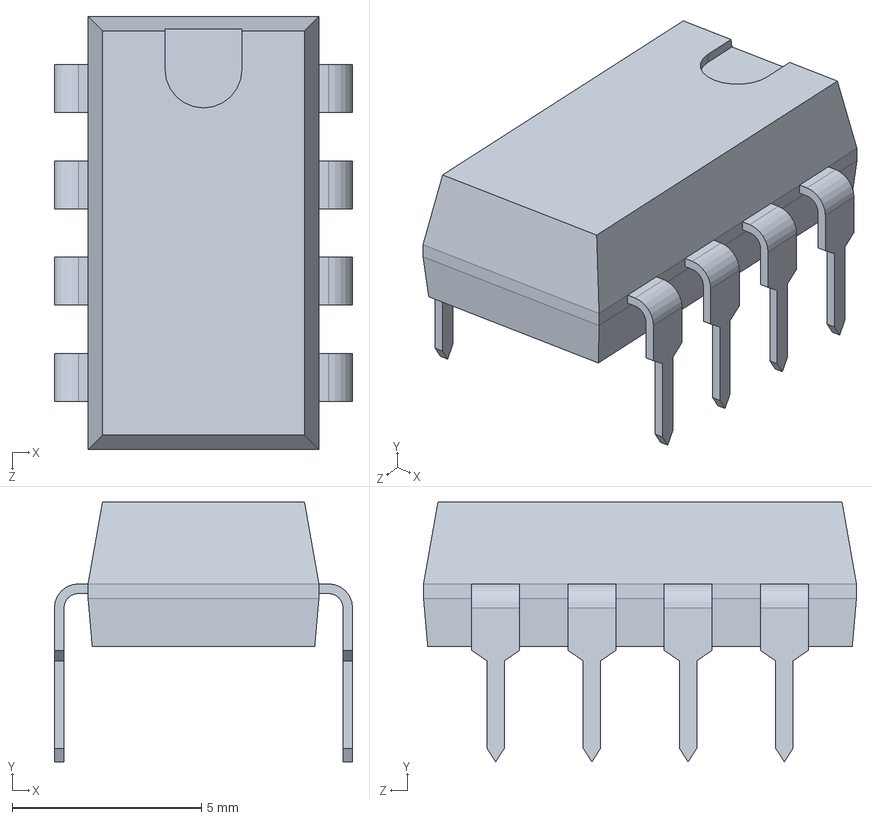
[picture p88: CAD file, 2015-12-23]
CAD/Platine/Bauteile/DIP8.SLDPRT
7.87 x 6.86 x 11.4 mm
