pfanchri/Wordclock/CAD/Platine/Bauteile/C0805.SLDPRT

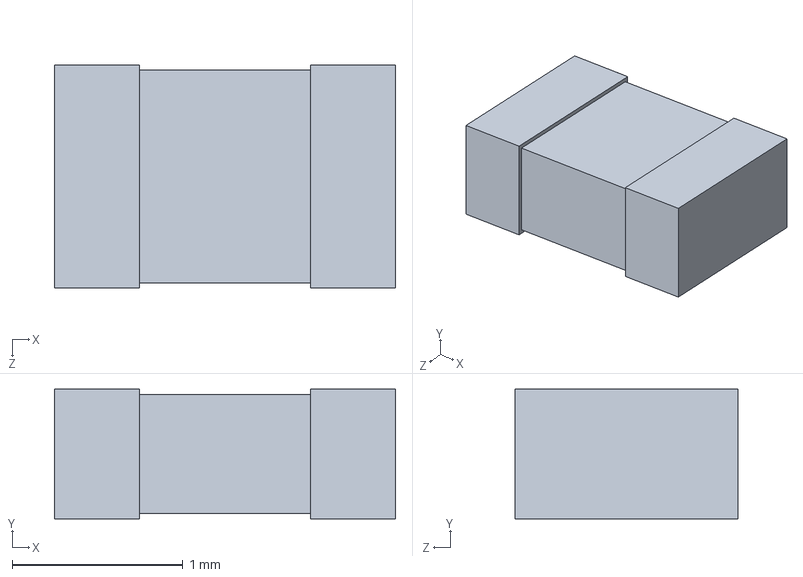
[picture p89: CAD file, 2015-12-23]
CAD/Platine/Bauteile/C0805.SLDPRT
2.00 x 0.76 x 1.31 mm
