pfanchri/Wordclock/CAD/Platine/Bauteile/HC49S.SLDPRT

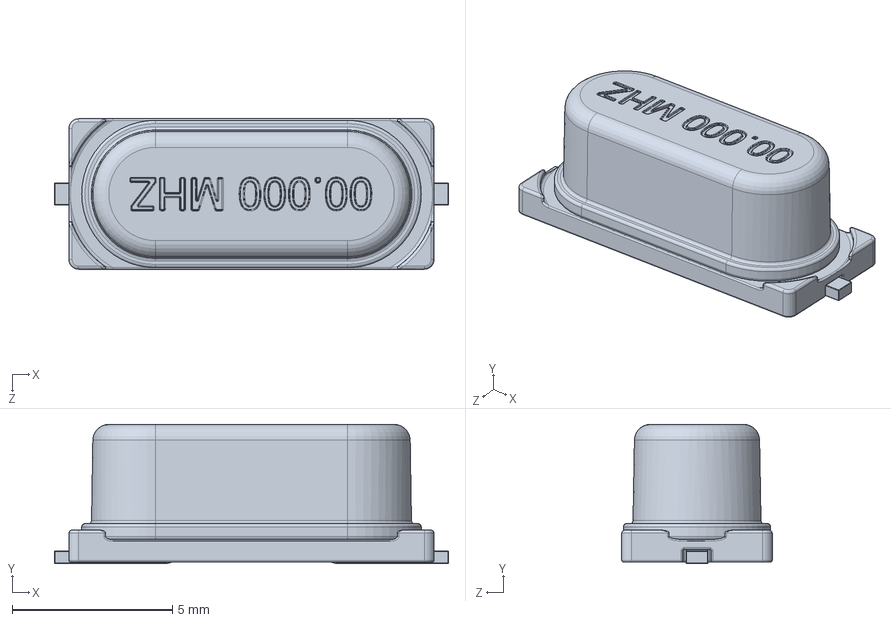
[picture p90: CAD file, 2015-12-23]
CAD/Platine/Bauteile/HC49S.SLDPRT
12.3 x 4.35 x 4.70 mm
