pfanchri/Wordclock/CAD/Platine/Bauteile/M1206.SLDPRT

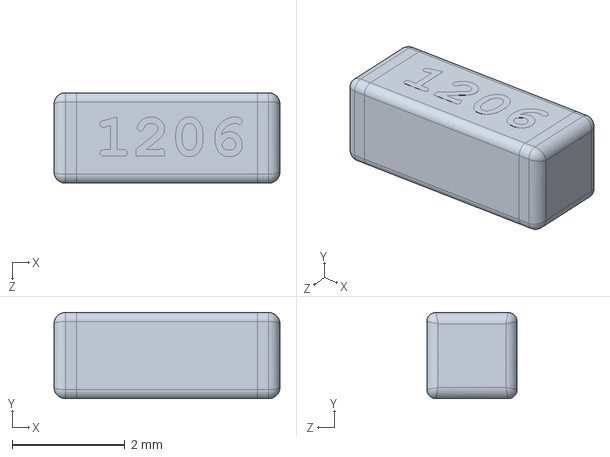
[picture p91: CAD file, 2015-12-23]
CAD/Platine/Bauteile/M1206.SLDPRT
4.00 x 1.53 x 1.60 mm
