pfanchri/Wordclock/CAD/Platine/Bauteile/C1310.SLDPRT

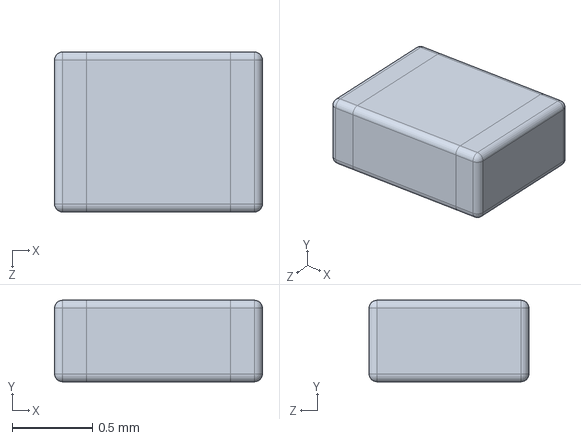
[picture p92: CAD file, 2015-12-23]
CAD/Platine/Bauteile/C1310.SLDPRT
1.30 x 0.51 x 1.00 mm
