pfanchri/Wordclock/CAD/Platine/Bauteile/Taster.SLDPRT

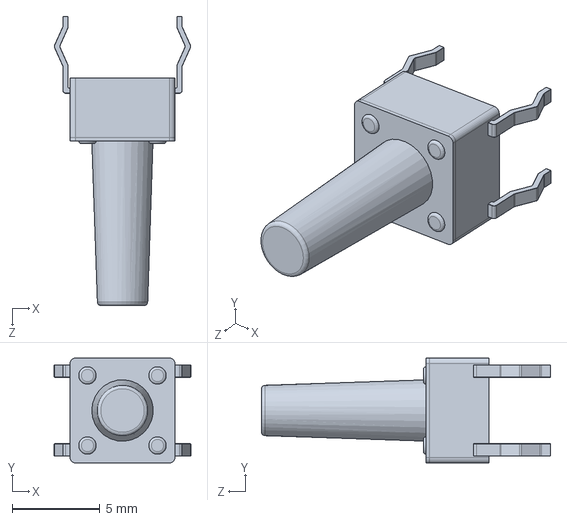
[picture p93: CAD file, 2015-12-23]
CAD/Platine/Bauteile/Taster.SLDPRT
7.80 x 5.99 x 16.5 mm
