pfanchri/Wordclock/CAD/Platine/Bauteile/C1206.SLDPRT

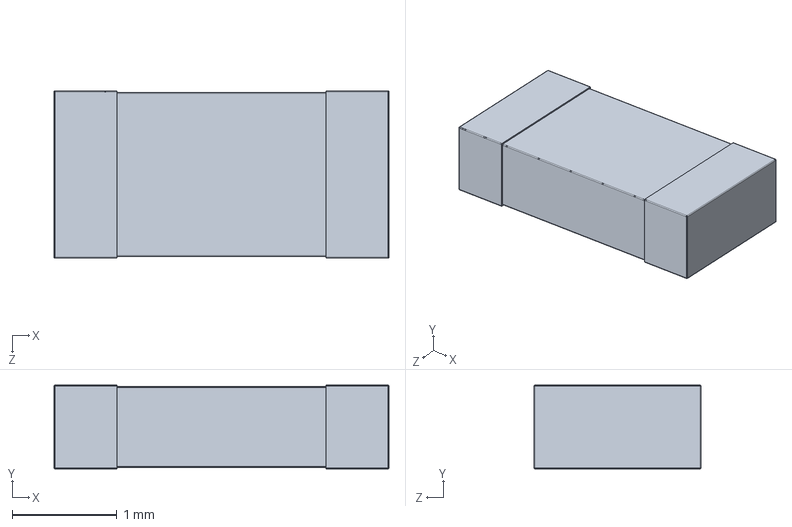
[picture p94: CAD file, 2015-12-23]
CAD/Platine/Bauteile/C1206.SLDPRT
3.20 x 0.8 x 1.60 mm
