pfanchri/Wordclock/CAD/Platine/Bauteile/DIP28.SLDPRT

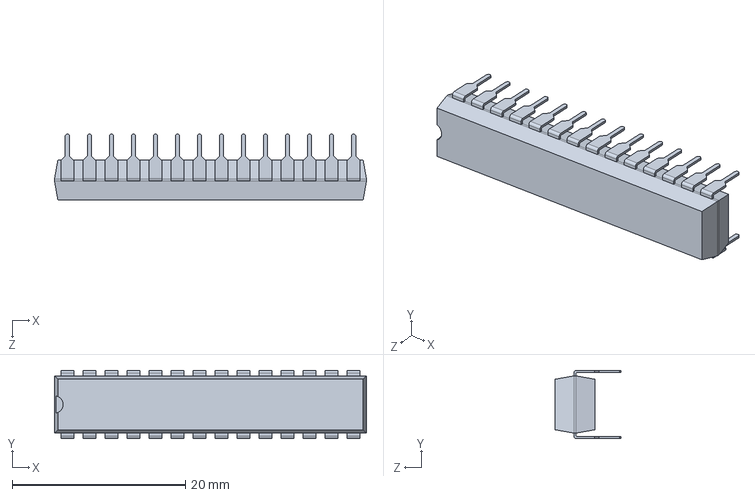
[picture p95: CAD file, 2015-12-23]
CAD/Platine/Bauteile/DIP28.SLDPRT
36.0 x 7.87 x 7.57 mm
