pfanchri/Wordclock/CAD/CircuitWorks/Komponenten/R1206_R1206.sldprt

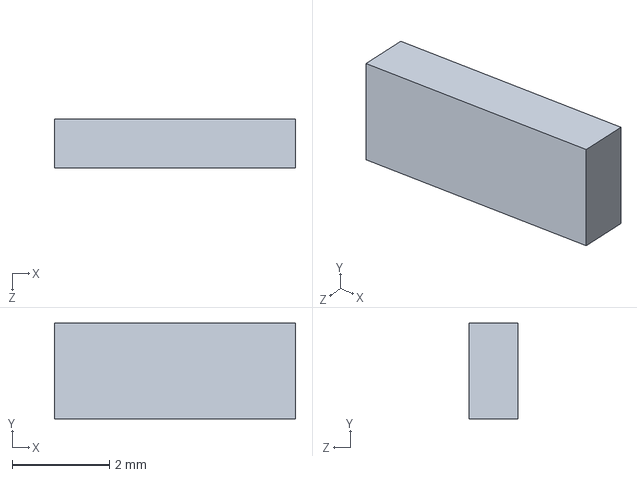
[picture p96: CAD file, 2015-12-23]
CAD/CircuitWorks/Komponenten/R1206_R1206.sldprt
4.95 x 1.97 x 1.00 mm
