pfanchri/Wordclock/CAD/Platine/Bauteile/DIP28 Sockel.SLDPRT

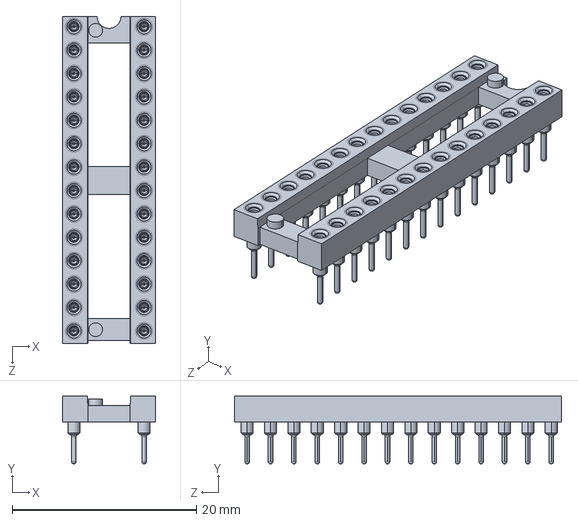
[picture p97: CAD file, 2015-12-23]
CAD/Platine/Bauteile/DIP28 Sockel.SLDPRT
10.1 x 7.37 x 35.5 mm
