pfanchri/Wordclock/CAD/CircuitWorks/Komponenten/M1206_M1206.sldprt

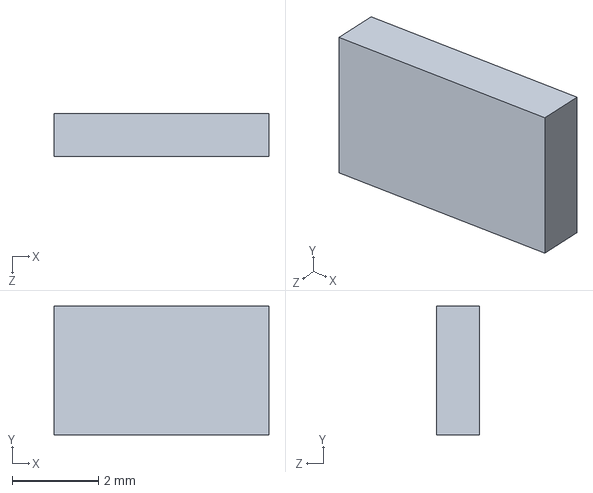
[picture p98: CAD file, 2015-12-23]
CAD/CircuitWorks/Komponenten/M1206_M1206.sldprt
5.00 x 2.99 x 1.00 mm
