pfanchri/Wordclock/CAD/Platine/Platinenmaße/Platinenmaße.PDF

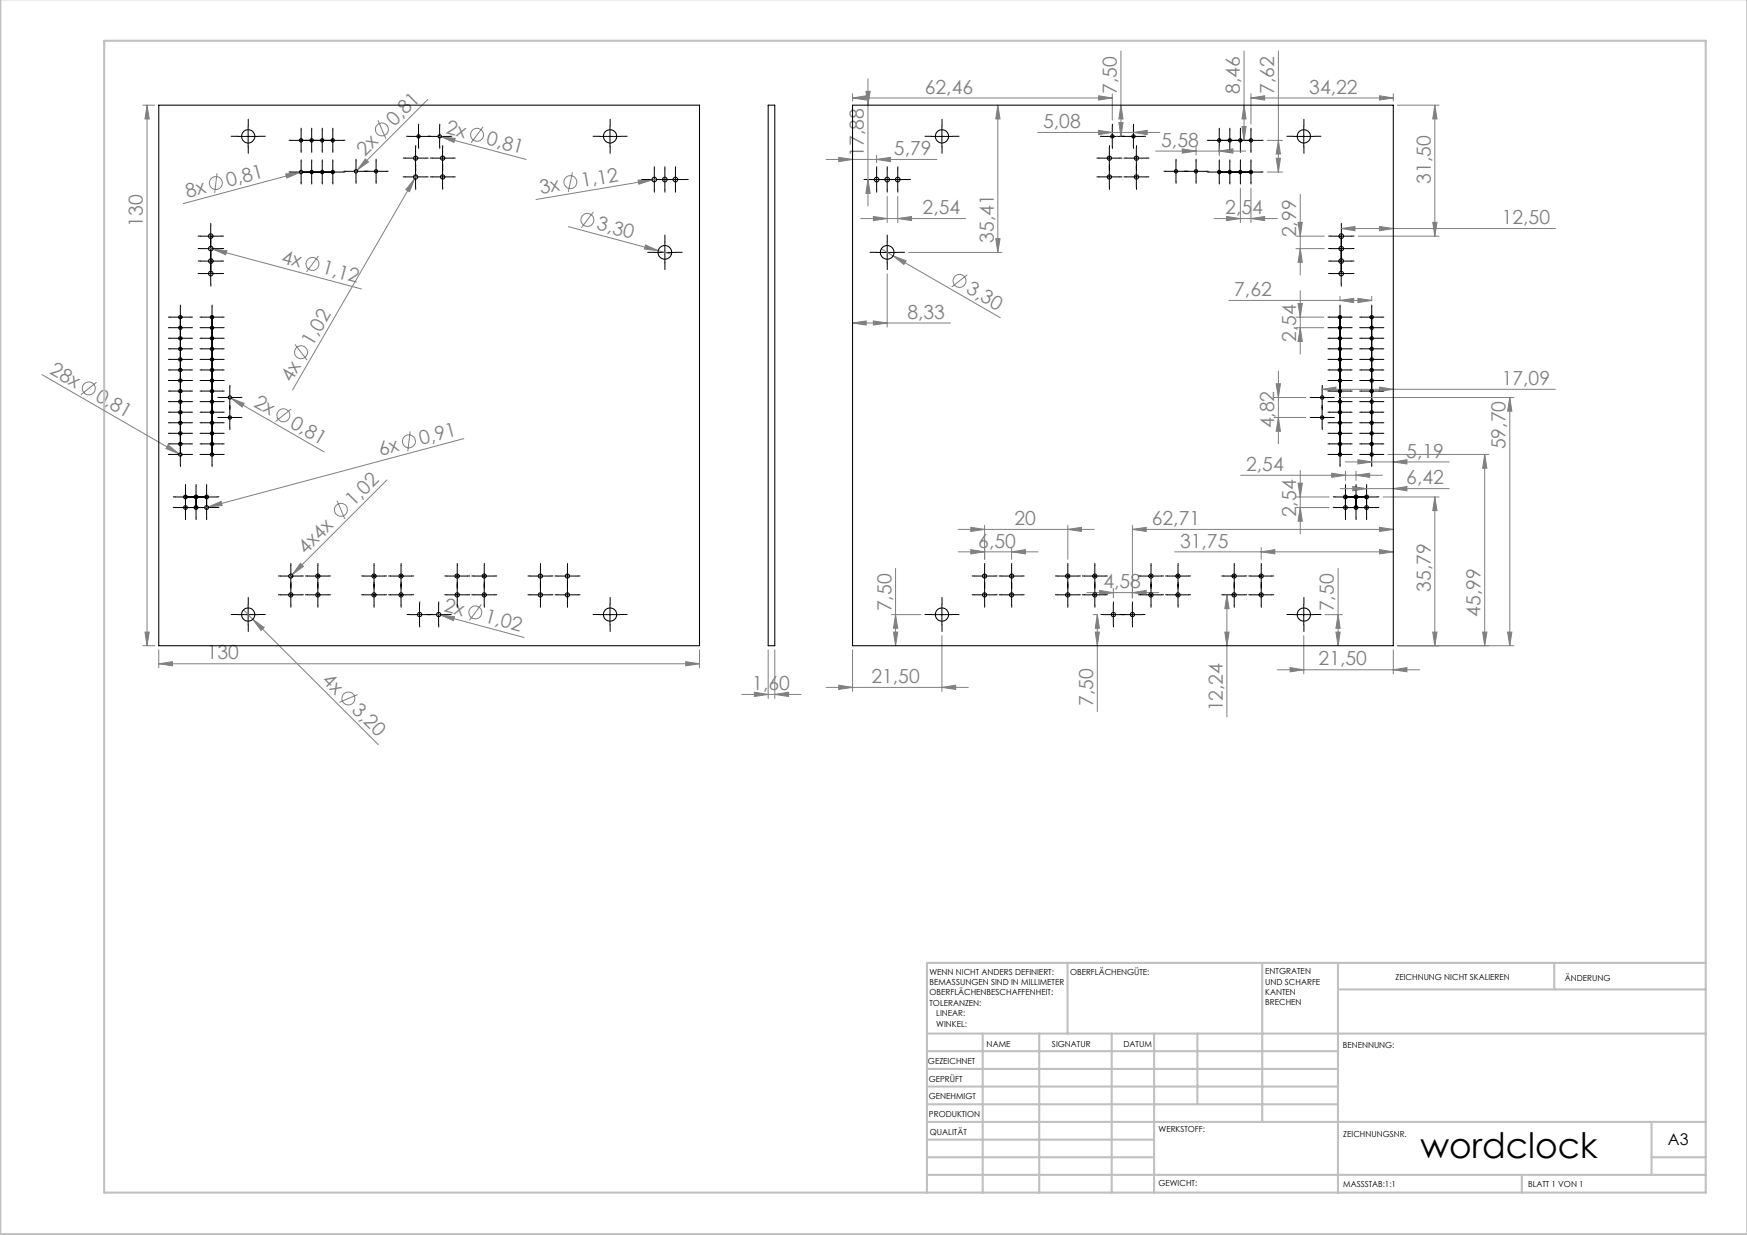
[picture p112: page 1]
MASSSTAB:1:1; BLATT 1 VON 1; ZEICHNUNG NICHT SKALIEREN; ÄNDERUNG; UND SCHARFE; WENN NICHT ANDERS DEFINIERT:; OBERFLÄCHENGÜTE:

BEMASSUNGEN SIND IN MILLIMETER
OBERFLÄCHENBESCHAFFENHEIT:
TOLERANZEN:
LINEAR:
WINKEL:

NAME | SIGNATUR | DATUM | | | | BENENNUNG:
QUALITÄT | | | | WERKSTOFF: | wordclock GEWICHT: ZEICHNUNGSNR. | A3

GEZEICHNET
GEPRÜFT
GENEHMIGT
PRODUKTION
