pfanchri/Wordclock/Eagle/Wordclock/Wordclock.pdf

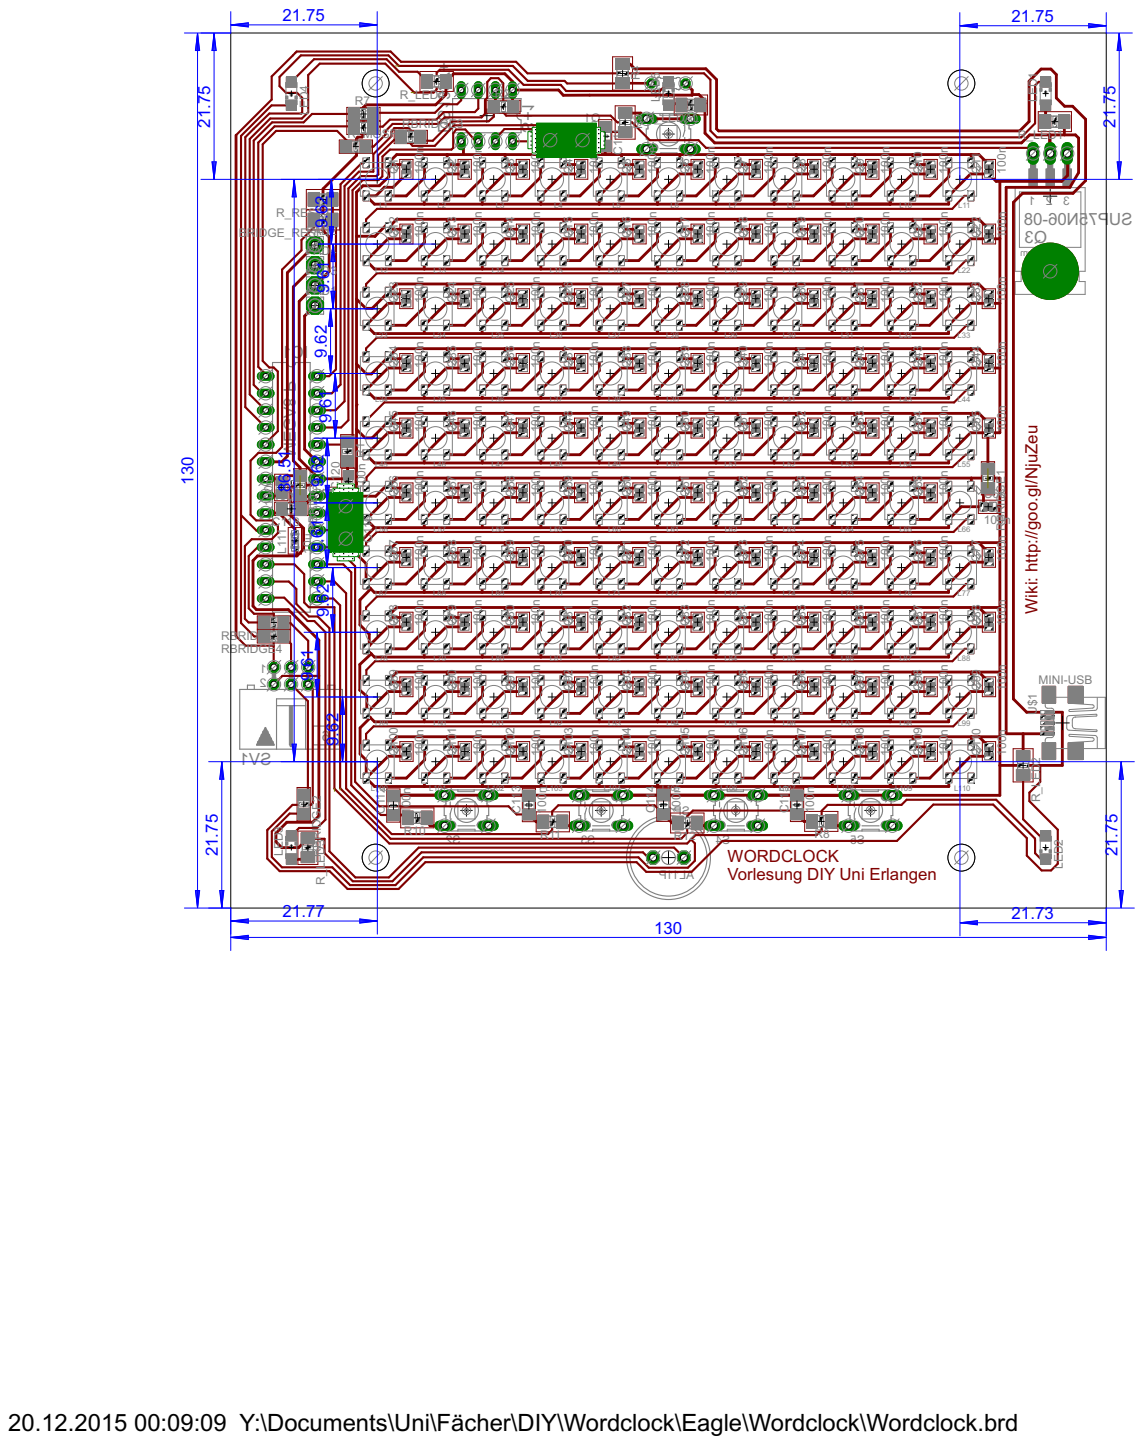
[picture p113: page 1]

Wiki: http://goo.gl/NjuZeu U$1

WORDCLOCK
Vorlesung DIY Uni Erlangen

20.12.2015 00:09:09 Y:\Documents\Uni\Fächer\DIY\Wordclock\Eagle\Wordclock\Wordclock.brd
